Safecast/Safecast-Air/docs/gas_and_particulate/_static/3.JPG

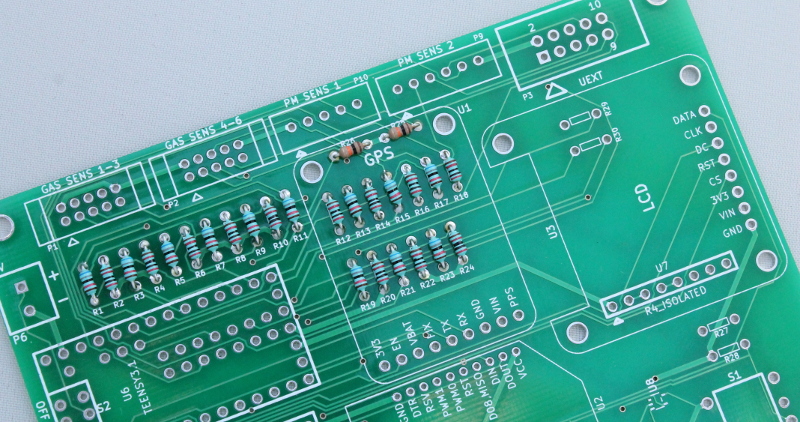
docs/gas_and_particulate/_static/3.JPG
