Safecast/Safecast-Air/docs/gas_and_particulate/_static/4.JPG

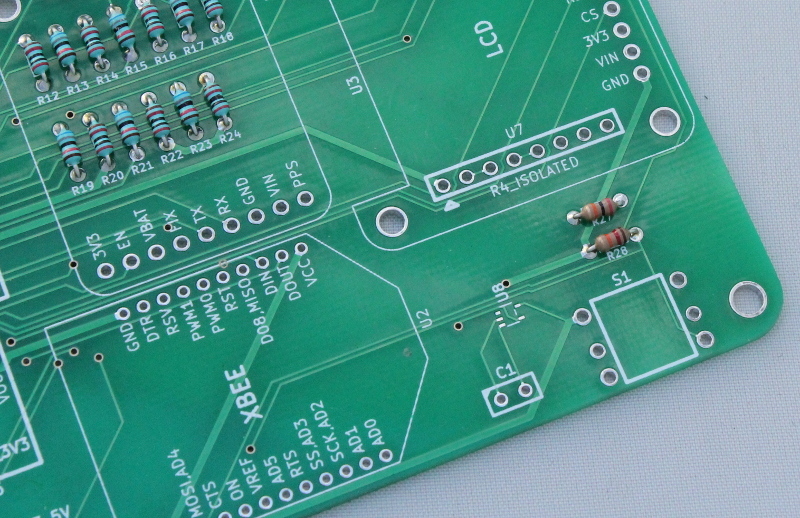
docs/gas_and_particulate/_static/4.JPG
