Safecast/Safecast-Air/docs/gas_and_particulate/_static/6.JPG

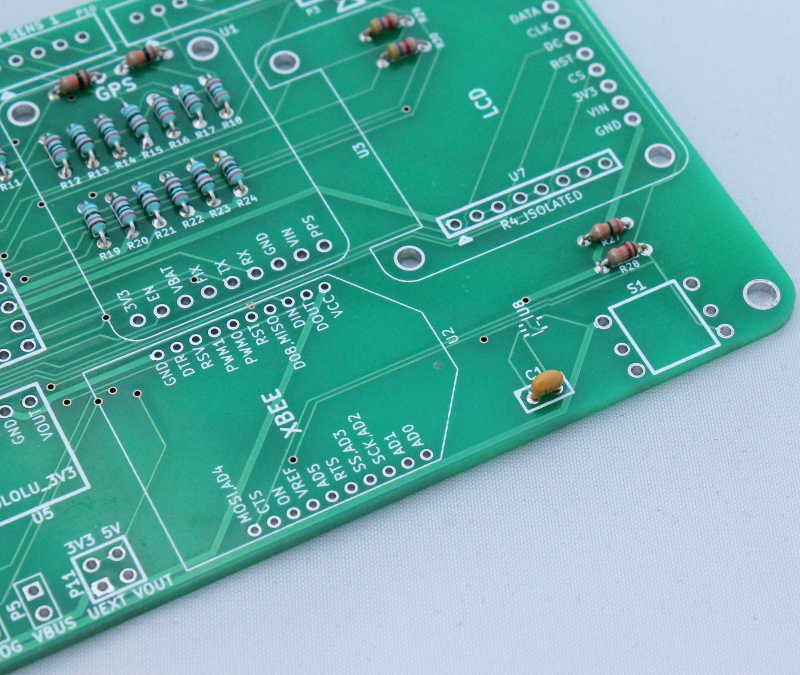
docs/gas_and_particulate/_static/6.JPG
