Safecast/Safecast-Air/docs/gas_and_particulate/_static/17c.JPG

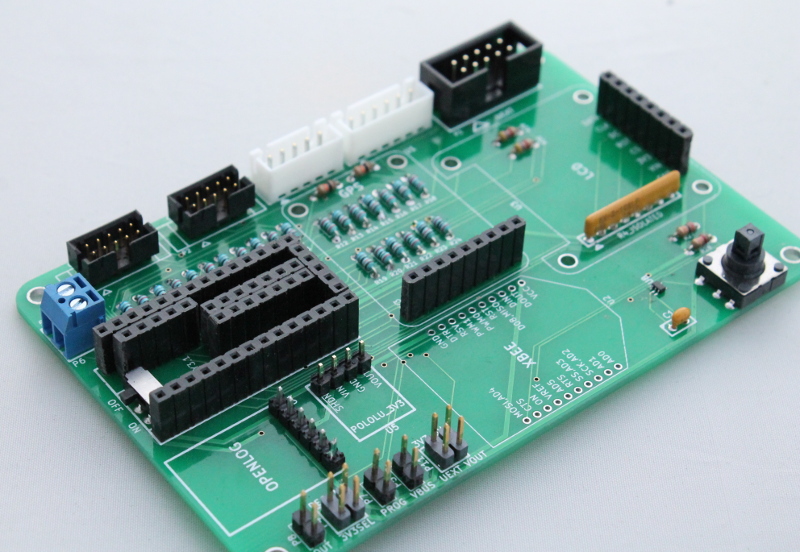
docs/gas_and_particulate/_static/17c.JPG
