Safecast/Safecast-Air/docs/gas_and_particulate/_static/21b.JPG

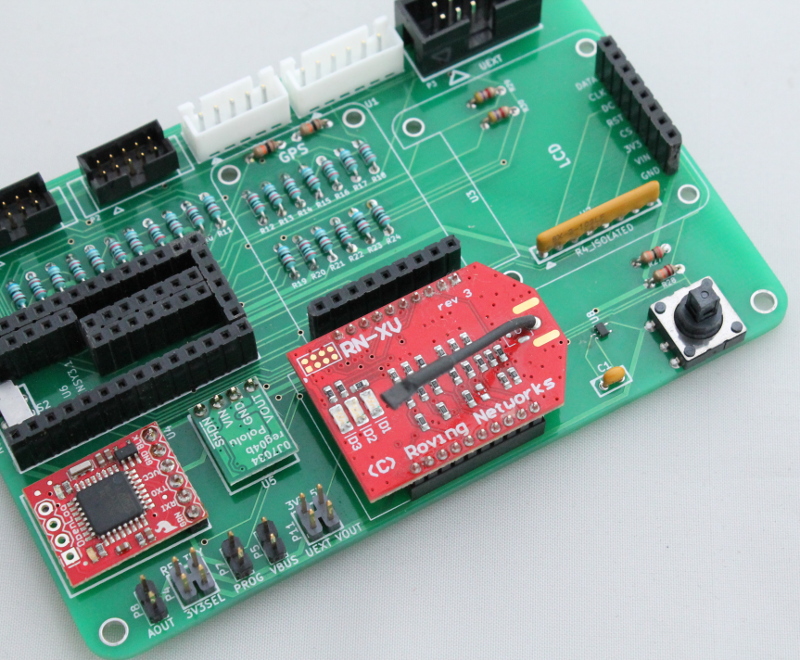
docs/gas_and_particulate/_static/21b.JPG
