Safecast/Safecast-Air/docs/gas_and_particulate/_static/alphasense_gas_1.png

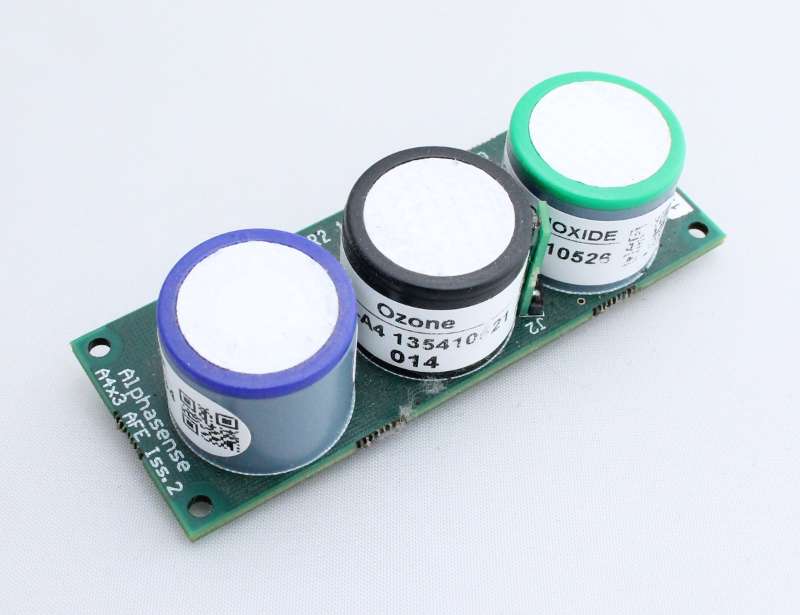
docs/gas_and_particulate/_static/alphasense_gas_1.png
