Safecast/Safecast-Air/docs/gas_and_particulate/_static/board_1.png

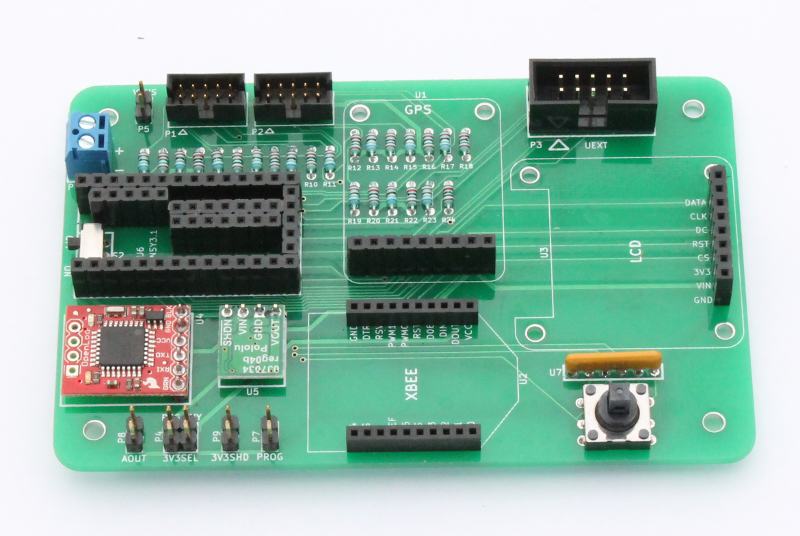
docs/gas_and_particulate/_static/board_1.png
