Safecast/Safecast-Air/docs/gas_and_particulate/_static/board_ver2.png

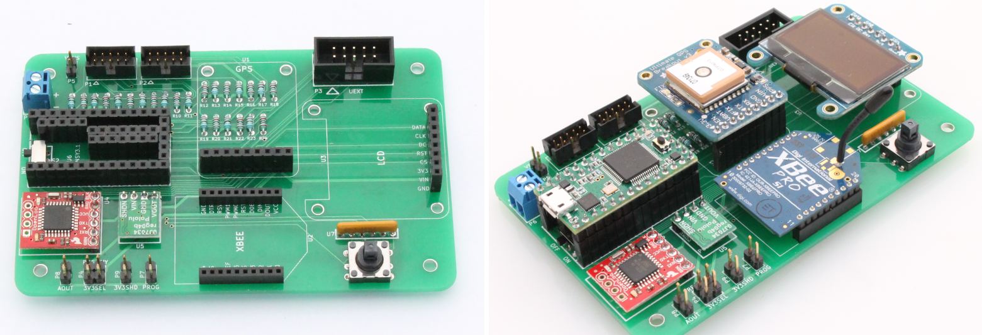
docs/gas_and_particulate/_static/board_ver2.png
