Safecast/Safecast-Air/docs/gas_and_particulate/_static/rev3_2.png

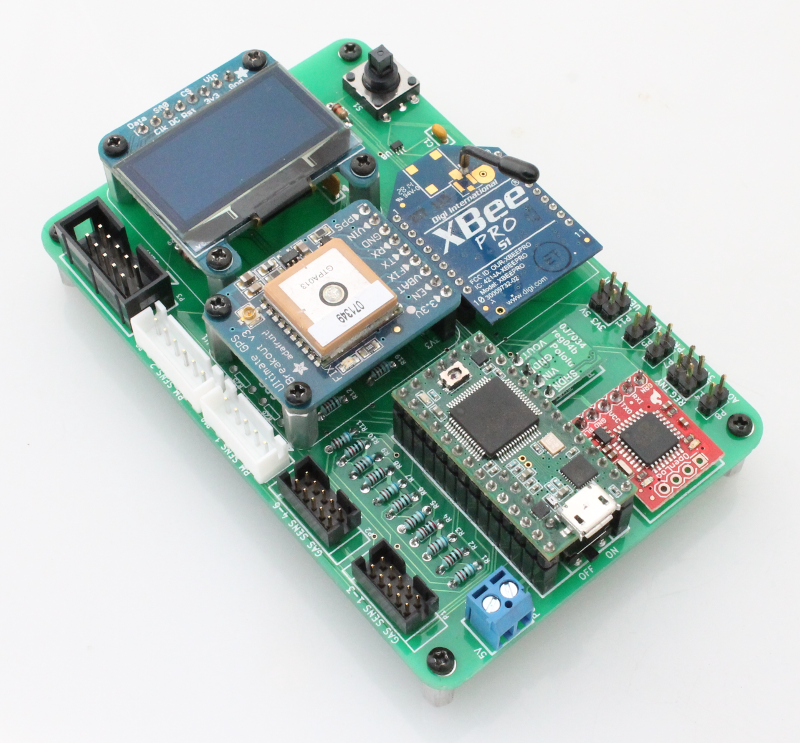
docs/gas_and_particulate/_static/rev3_2.png
