Safecast/Safecast-Air/docs/gas_and_particulate/_static/v4_7a.png

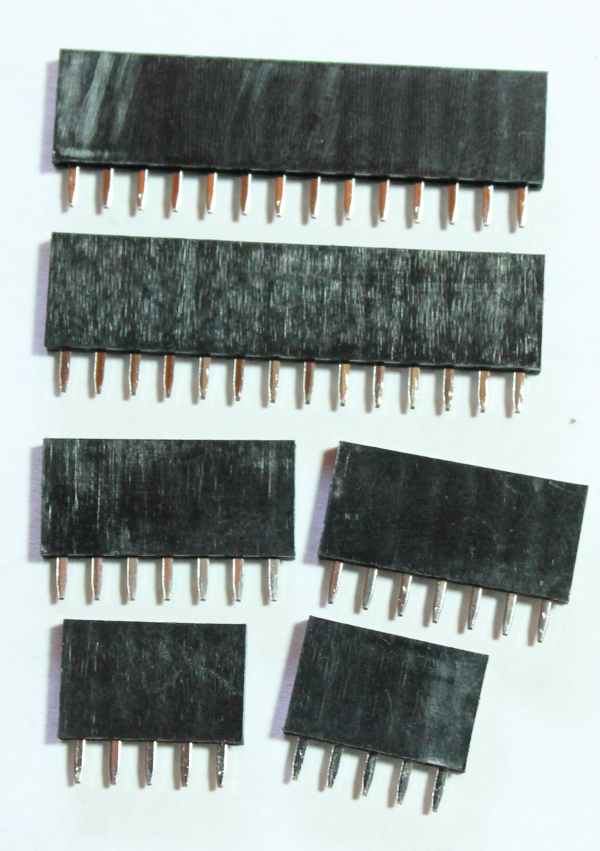
docs/gas_and_particulate/_static/v4_7a.png
