Safecast/Safecast-Air/images/about-arduino.png

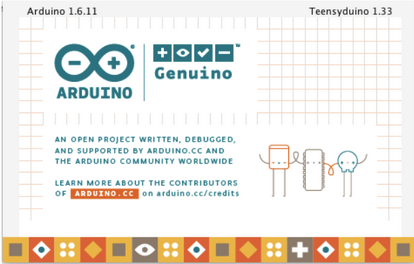
images/about-arduino.png
