Safecast/Safecast-Air/images/arduino.png

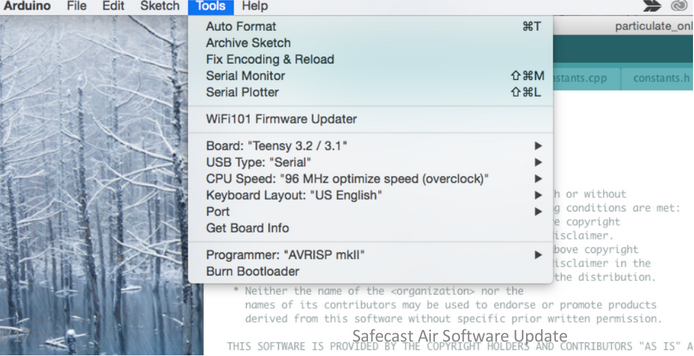
images/arduino.png
