Safecast/Safecast-Air/images/clone.png

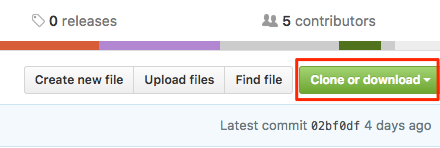
images/clone.png
