Safecast/Safecast-Air/images/electronics-assembly/schematic-small.png

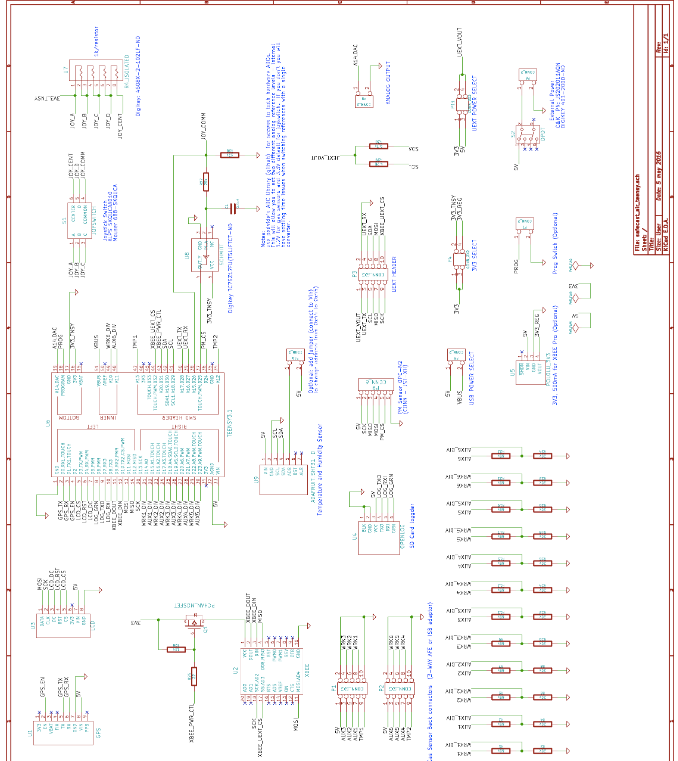
images/electronics-assembly/schematic-small.png
