Safecast/Safecast-Air/images/github-breadcrumb-link.png

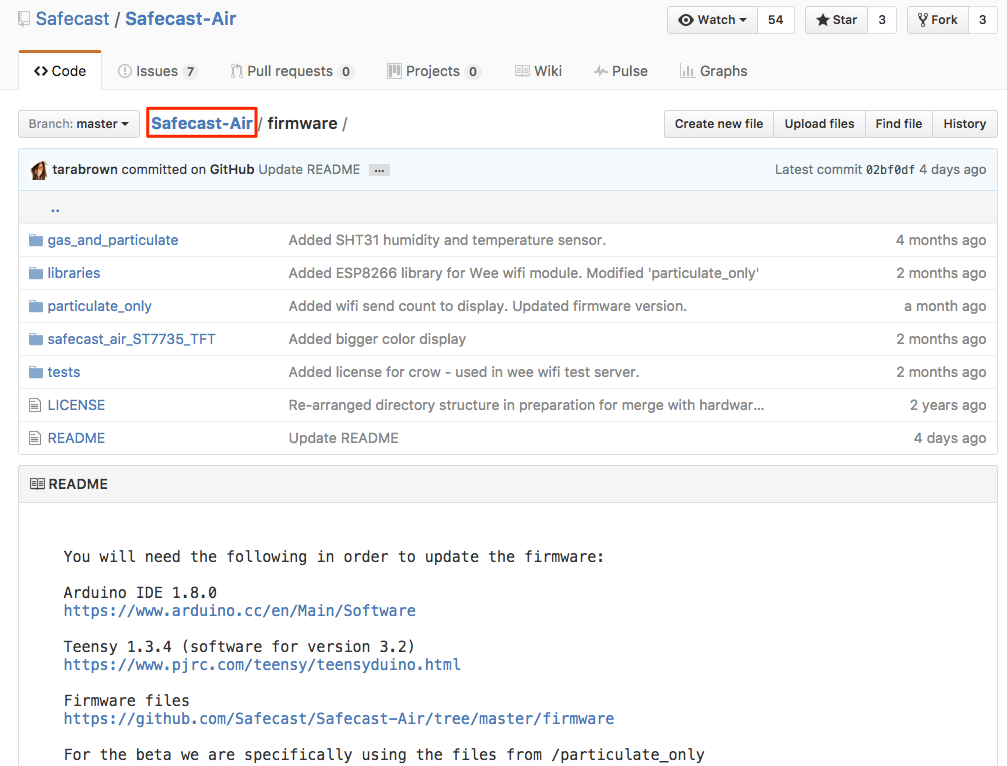
images/github-breadcrumb-link.png
