Safecast/Safecast-Air/images/log-file-detail.png

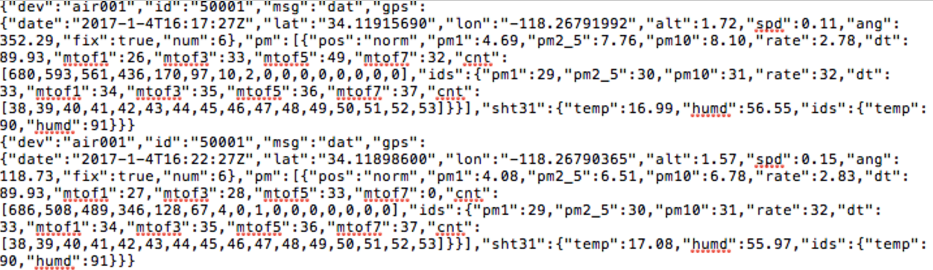
images/log-file-detail.png
