Safecast/Safecast-Air/images/log-files.png

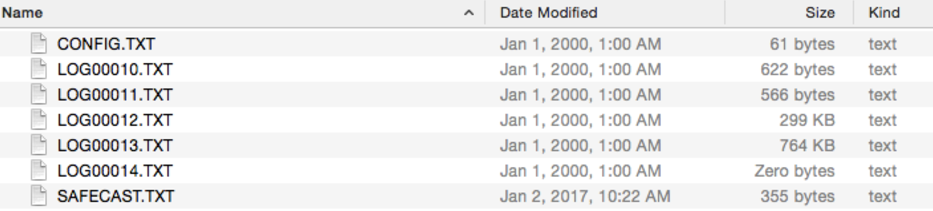
images/log-files.png
