Safecast/Safecast-Air/images/safecast-air-display.JPG

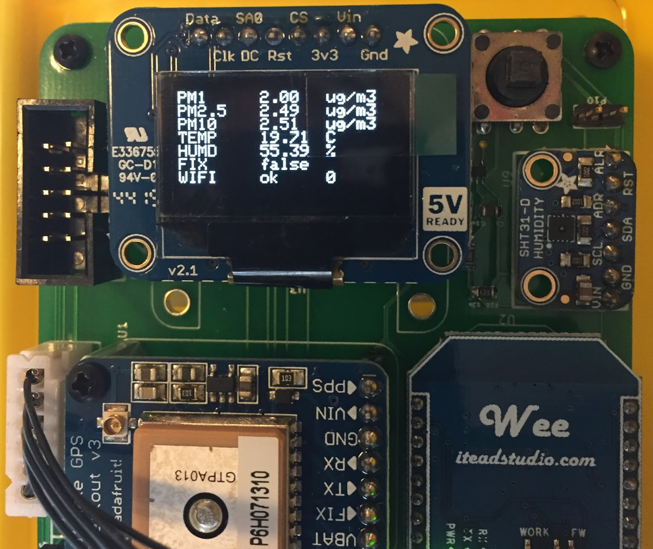
images/safecast-air-display.JPG
