Safecast/Safecast-Air/images/safecast-txt.png

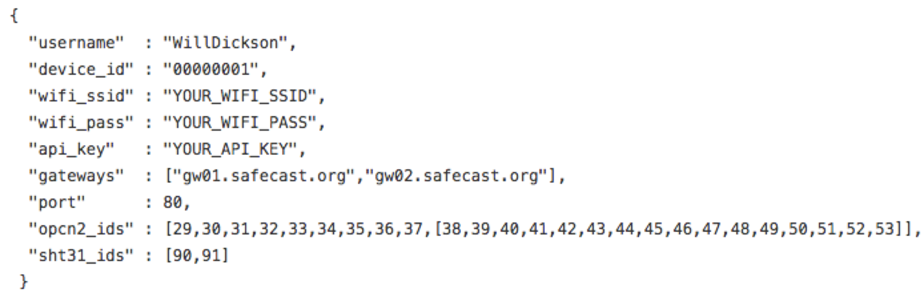
images/safecast-txt.png
