Safecast/Safecast-Air/images/safecast.png

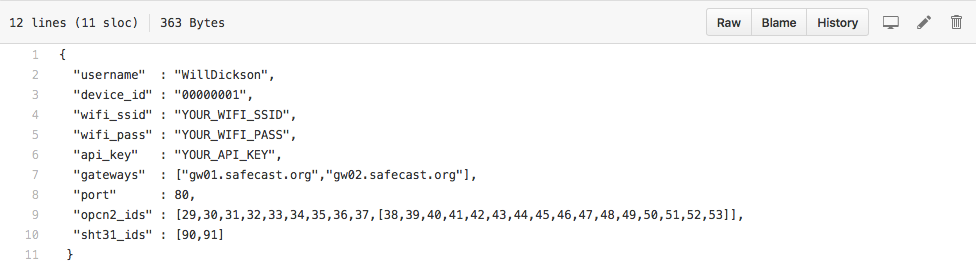
images/safecast.png
