Safecast/Safecast-Air/images/sketch.png

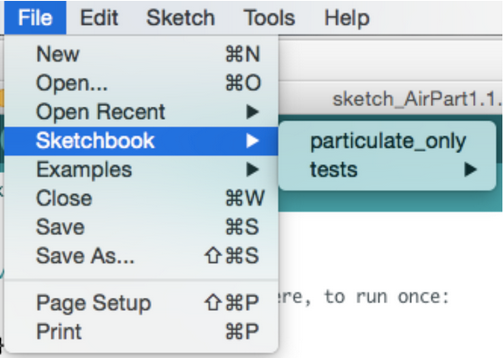
images/sketch.png
