Safecast/Safecast-Air/images/teensy-folders.png

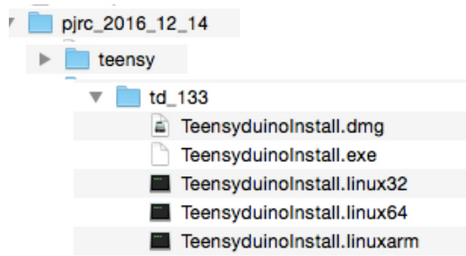
images/teensy-folders.png
