Safecast/Safecast-Air/images/teensy-tools-menu.png

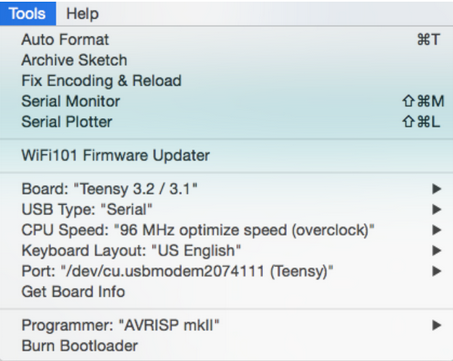
images/teensy-tools-menu.png
