Safecast/Safecast-Air/images/upload-sketch.png

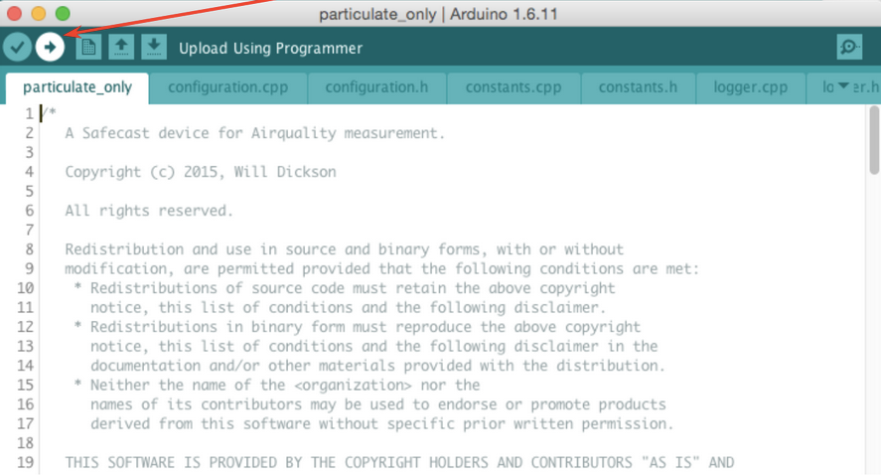
images/upload-sketch.png
