Safecast/Safecast-Air/images/usb.png

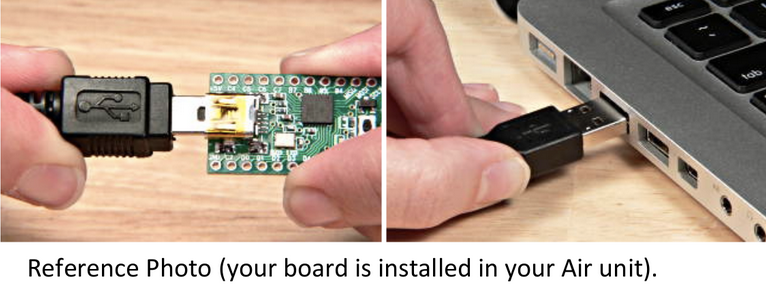
images/usb.png
