Safecast/Safecast-Air/images/zip.png

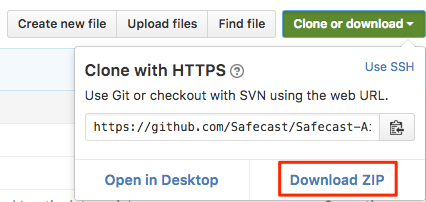
images/zip.png
