Safecast/Safecast-Air/images/electronics-assembly/main-board-first-set-components.png

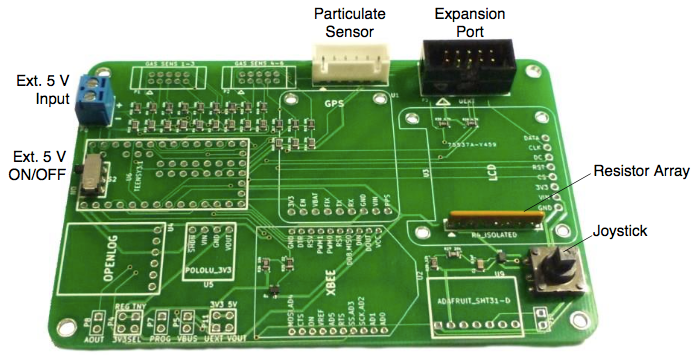
images/electronics-assembly/main-board-first-set-components.png
