Safecast/Safecast-Air/images/electronics-assembly/parts-bagged.png

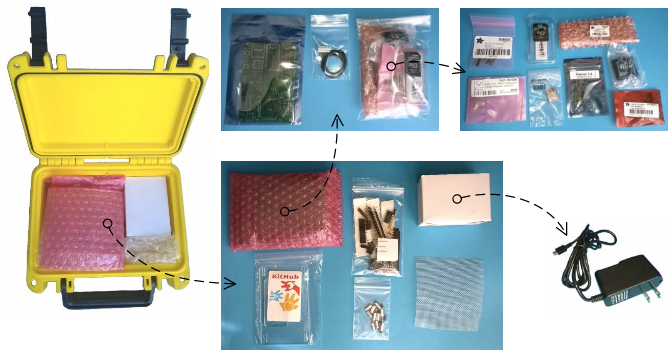
images/electronics-assembly/parts-bagged.png
