Safecast/Safecast-Air/hardware/enclosure/seahorse_120/methane_only/lower_insert/lower_insert.dxf

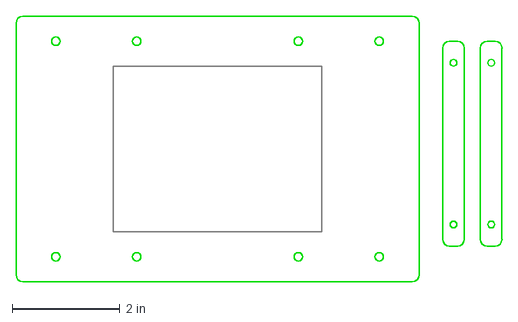
[picture p119: CAD file, 2016-02-19]
hardware/enclosure/seahorse_120/methane_only/lower_insert/lower_insert.dxf
9.02 x 4.92 in
