Safecast/Safecast-Air/hardware/enclosure/seahorse_120/methane_only/upper_insert/upper_insert.dxf

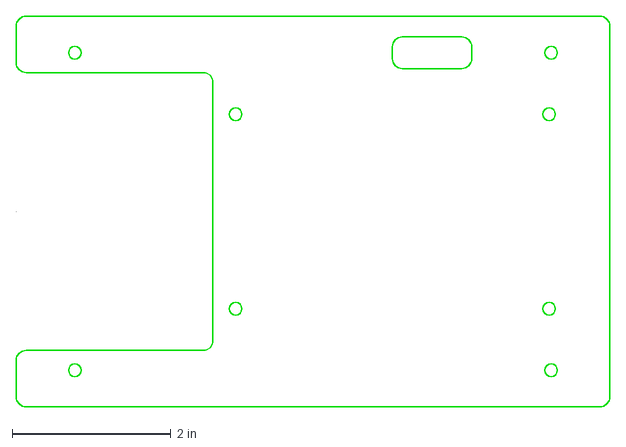
[picture p120: CAD file, 2016-02-19]
hardware/enclosure/seahorse_120/methane_only/upper_insert/upper_insert.dxf
7.48 x 4.92 in
