Safecast/Safecast-Air/hardware/enclosure/budind_nema_nbb/faraday/faraday_side_2.dxf

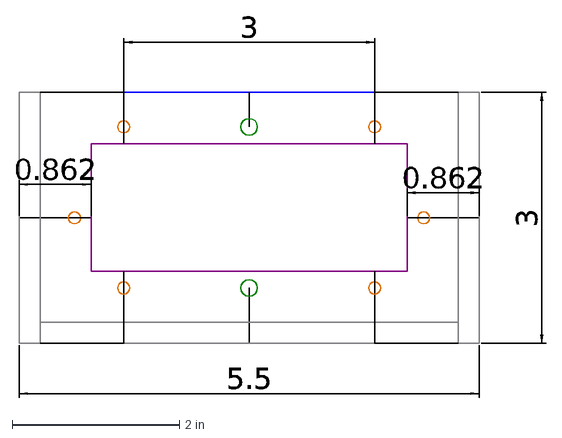
[picture p121: CAD file, 2015-12-14]
hardware/enclosure/budind_nema_nbb/faraday/faraday_side_2.dxf
5.5
3
0.862
