Safecast/Safecast-Air/hardware/enclosure/budind_nema_nbb/layouts/lasercutting/bottom_layout/pilot_template.dxf

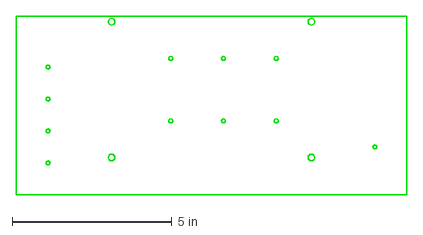
[picture p122: CAD file, 2015-09-15]
hardware/enclosure/budind_nema_nbb/layouts/lasercutting/bottom_layout/pilot_template.dxf
12.2 x 5.59 in
