Safecast/Safecast-Air/hardware/enclosure/layouts/isb_adaptor.dxf

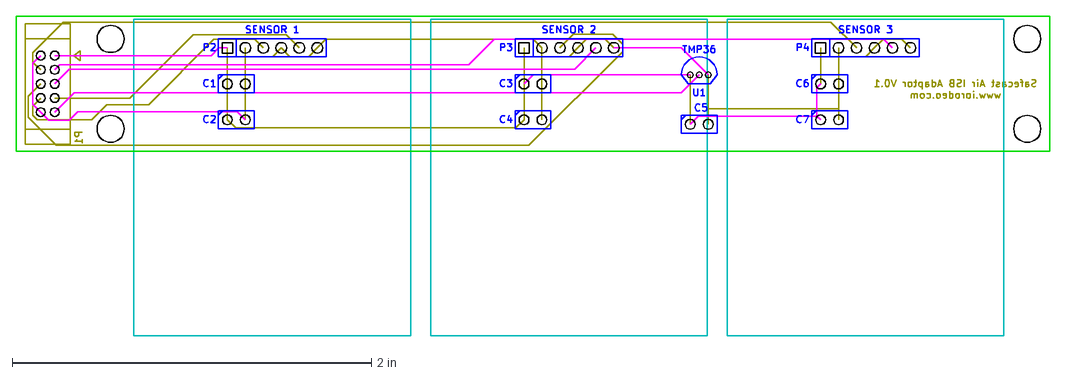
[picture p123: CAD file, 2015-06-25]
hardware/enclosure/layouts/isb_adaptor.dxf
5.75 x 1.77 in
