Safecast/Safecast-Air/hardware/enclosure/budind_nema_nbb/faraday/faraday_floor.dxf

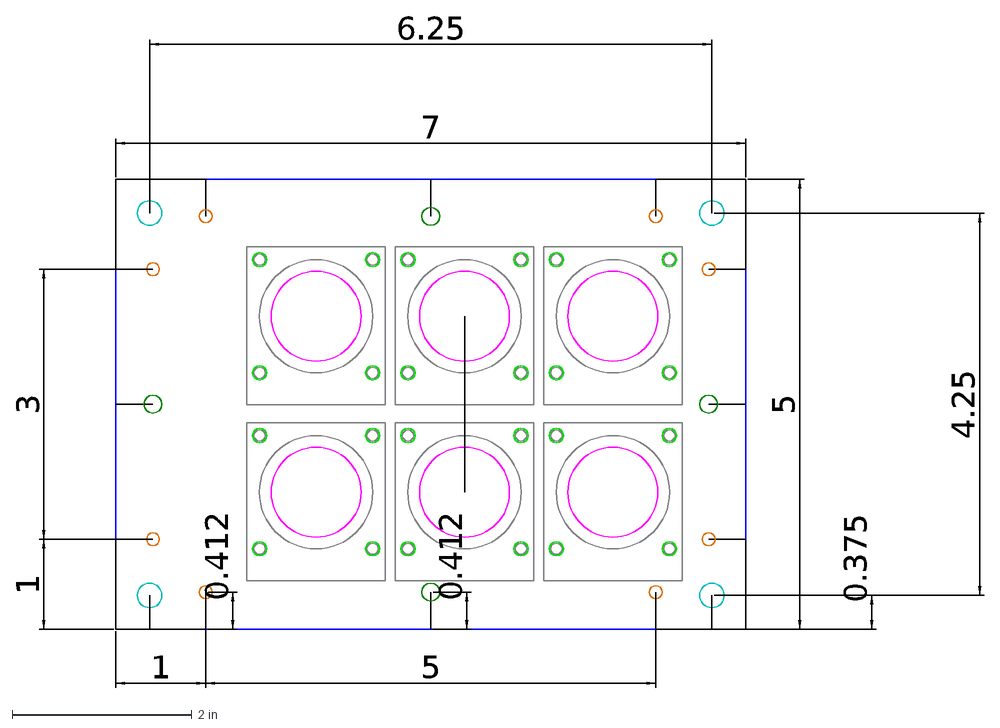
[picture p124: CAD file, 2015-09-15]
hardware/enclosure/budind_nema_nbb/faraday/faraday_floor.dxf
7
5
1
0.412
3
0.375
6.25
4.25
