Safecast/Safecast-Air/hardware/enclosure/budind_nema_nbb/layouts/lasercutting/bottom_layout/combined_template.dxf

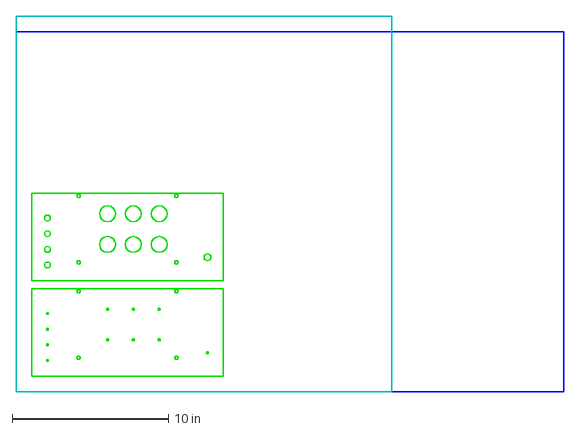
[picture p125: CAD file, 2015-09-15]
hardware/enclosure/budind_nema_nbb/layouts/lasercutting/bottom_layout/combined_template.dxf
35.0 x 24.0 in
