Safecast/Safecast-Air/hardware/enclosure/budind_nema_nbb/faraday/faraday_side_1.dxf

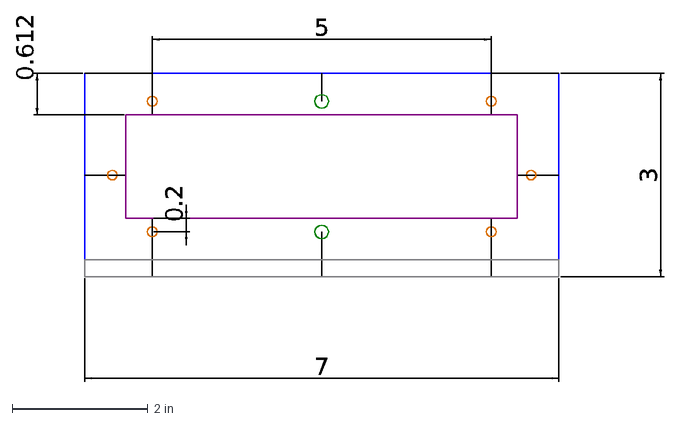
[picture p126: CAD file, 2015-09-01]
hardware/enclosure/budind_nema_nbb/faraday/faraday_side_1.dxf
3
7
0.2
5
0.612
