Safecast/Safecast-Air/hardware/enclosure/budind_nema_nbb/faraday/faraday_mesh_upper.dxf

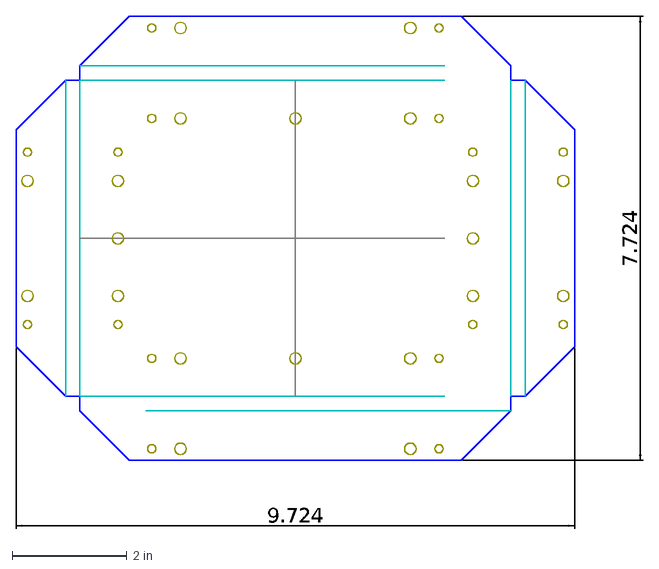
[picture p127: CAD file, 2015-09-01]
hardware/enclosure/budind_nema_nbb/faraday/faraday_mesh_upper.dxf
7.724
9.724
