Safecast/Safecast-Air/hardware/enclosure/budind_nema_nbb/faraday/faraday_mesh_lower.dxf

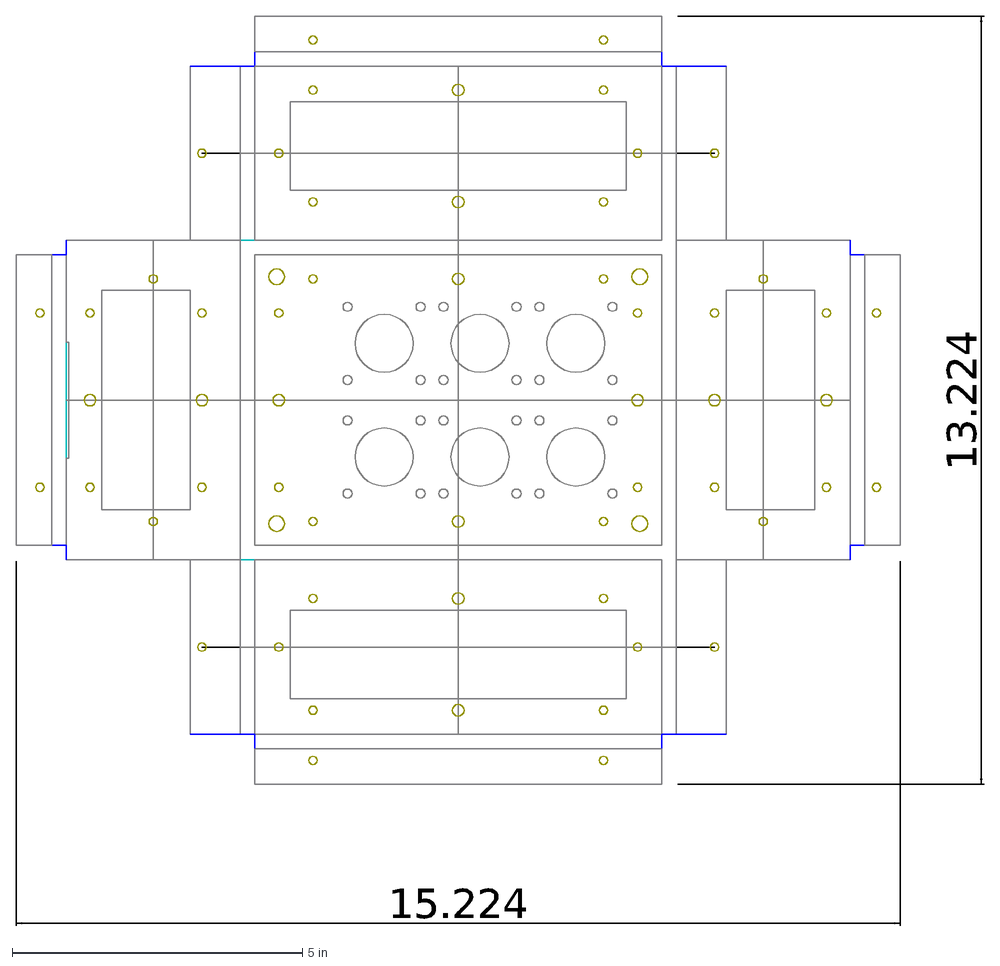
[picture p128: CAD file, 2015-08-30]
hardware/enclosure/budind_nema_nbb/faraday/faraday_mesh_lower.dxf
13.224
15.224
