Safecast/Safecast-Air/hardware/enclosure/budind_nema_nbb/faraday/faraday_side_3.dxf

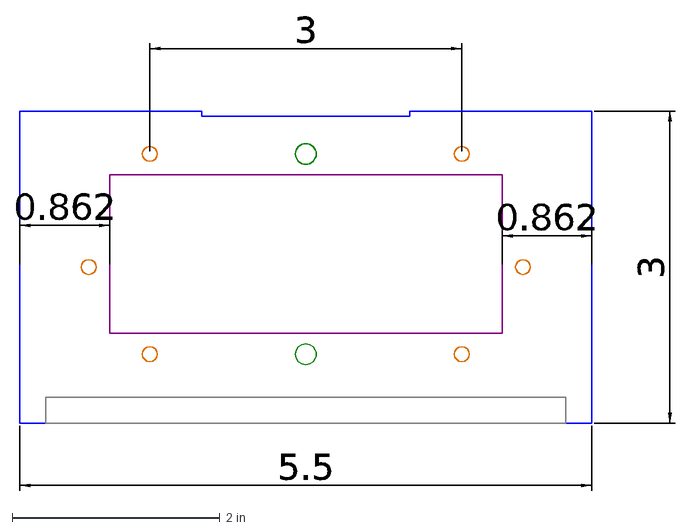
[picture p129: CAD file, 2015-08-30]
hardware/enclosure/budind_nema_nbb/faraday/faraday_side_3.dxf
5.5
3
0.862
