Safecast/Safecast-Air/hardware/enclosure/budind_nema_nbb/faraday/isb_footprint.dxf

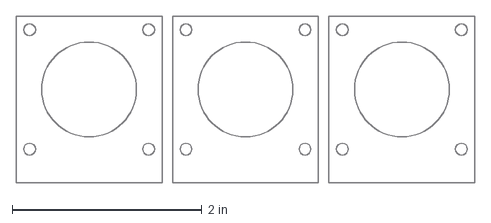
[picture p130: CAD file, 2015-08-06]
hardware/enclosure/budind_nema_nbb/faraday/isb_footprint.dxf
4.84 x 1.76 in
