Safecast/Safecast-Air/images/electronics-assembly/5v.png

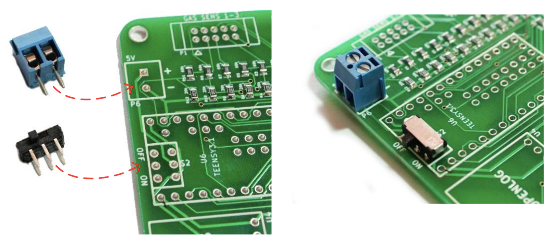
images/electronics-assembly/5v.png
