Safecast/Safecast-Air/images/electronics-assembly/14pos-headers-in-place.png

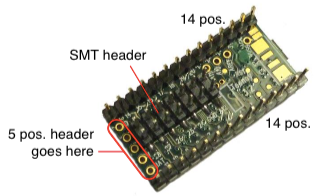
images/electronics-assembly/14pos-headers-in-place.png
