Safecast/Safecast-Air/images/electronics-assembly/ac wires-secured-with-a-cable-tie.png

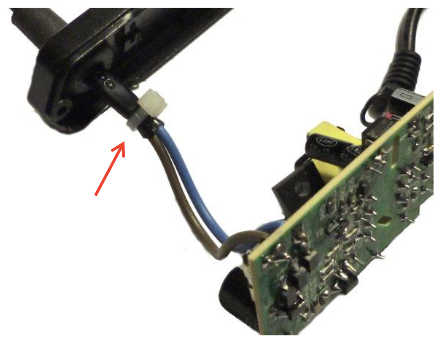
images/electronics-assembly/ac wires-secured-with-a-cable-tie.png
