Safecast/Safecast-Air/images/electronics-assembly/ac-power-cord-with-2-pin-Europlug.png

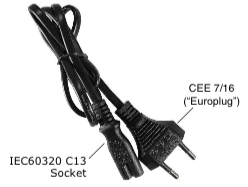
images/electronics-assembly/ac-power-cord-with-2-pin-Europlug.png
