Safecast/Safecast-Air/images/electronics-assembly/ac-wires-removed-from-PCB.png

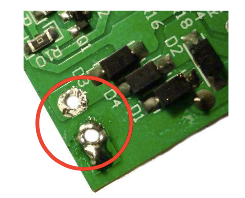
images/electronics-assembly/ac-wires-removed-from-PCB.png
