Safecast/Safecast-Air/images/electronics-assembly/adafruit-temp-humidity.png

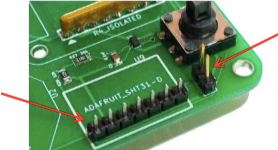
images/electronics-assembly/adafruit-temp-humidity.png
