Safecast/Safecast-Air/images/electronics-assembly/battery-clip-soldering.png

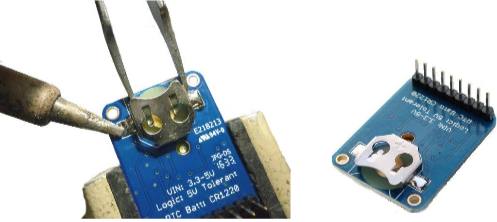
images/electronics-assembly/battery-clip-soldering.png
