Safecast/Safecast-Air/images/electronics-assembly/blades-removal-steps.png

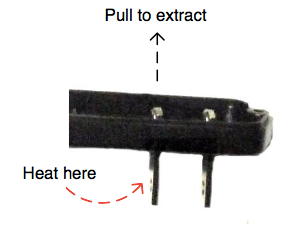
images/electronics-assembly/blades-removal-steps.png
