Safecast/Safecast-Air/images/electronics-assembly/cleaned-pcb.png

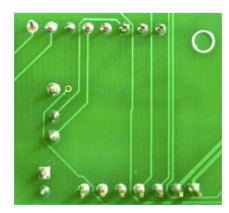
images/electronics-assembly/cleaned-pcb.png
