Safecast/Safecast-Air/images/electronics-assembly/completed-teensy-board.png

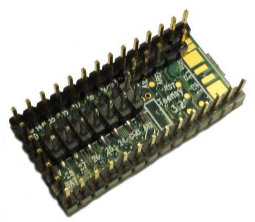
images/electronics-assembly/completed-teensy-board.png
