Safecast/Safecast-Air/images/electronics-assembly/config-presetting-headers-pcb-pos.png

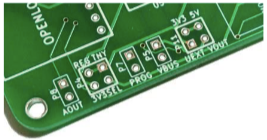
images/electronics-assembly/config-presetting-headers-pcb-pos.png
