Safecast/Safecast-Air/images/electronics-assembly/configuration-headers-in-place.png

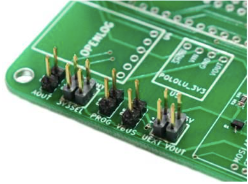
images/electronics-assembly/configuration-headers-in-place.png
