Safecast/Safecast-Air/images/electronics-assembly/cutting-away-the-socket.png

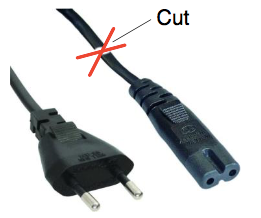
images/electronics-assembly/cutting-away-the-socket.png
