Safecast/Safecast-Air/images/electronics-assembly/cutting-straight-headers.png

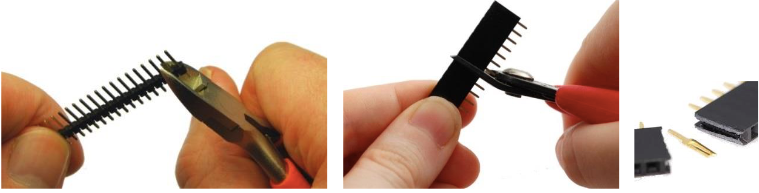
images/electronics-assembly/cutting-straight-headers.png
