Safecast/Safecast-Air/images/electronics-assembly/finished-board.png

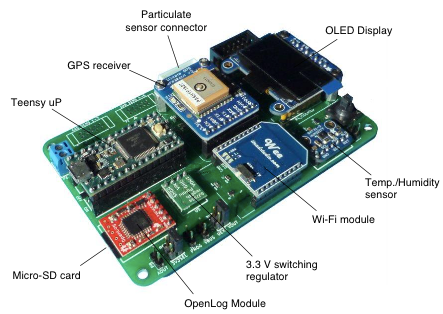
images/electronics-assembly/finished-board.png
