Safecast/Safecast-Air/images/electronics-assembly/gps-board-with-headers-back.png

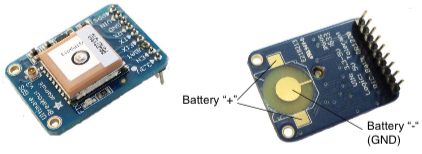
images/electronics-assembly/gps-board-with-headers-back.png
