Safecast/Safecast-Air/images/electronics-assembly/gps-complete-kit.png

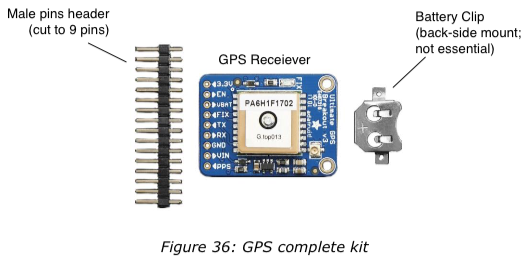
images/electronics-assembly/gps-complete-kit.png
