Safecast/Safecast-Air/images/electronics-assembly/gps-module-mounted.png

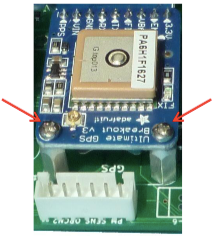
images/electronics-assembly/gps-module-mounted.png
