Safecast/Safecast-Air/images/electronics-assembly/gps-mounting.png

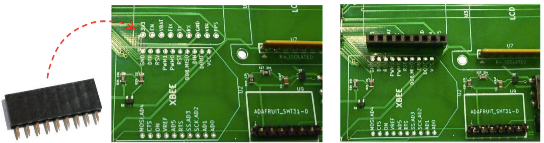
images/electronics-assembly/gps-mounting.png
