Safecast/Safecast-Air/images/electronics-assembly/Installed-OLED-Display.png

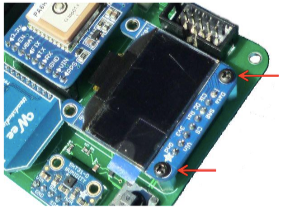
images/electronics-assembly/Installed-OLED-Display.png
