Safecast/Safecast-Air/images/electronics-assembly/main-board-mounted-on-acrylic-plate.png

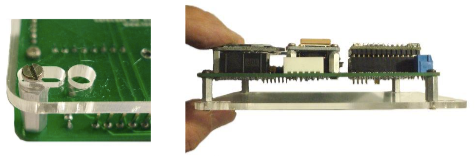
images/electronics-assembly/main-board-mounted-on-acrylic-plate.png
