Safecast/Safecast-Air/images/electronics-assembly/main-board-with-standoffs.png

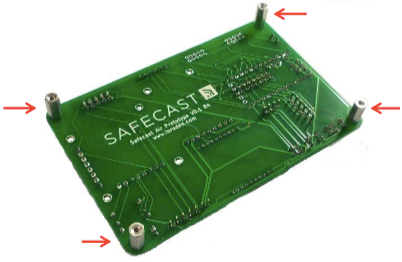
images/electronics-assembly/main-board-with-standoffs.png
