Safecast/Safecast-Air/images/electronics-assembly/main-pcb-layout.png

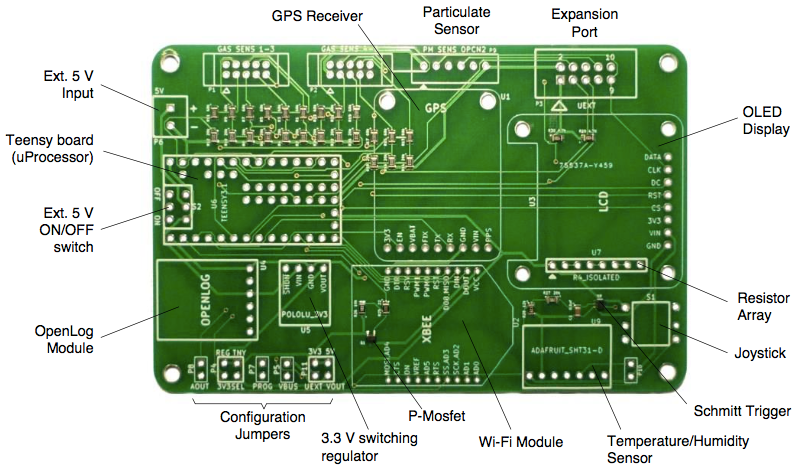
images/electronics-assembly/main-pcb-layout.png
