Safecast/Safecast-Air/images/electronics-assembly/misaligned-end-header.png

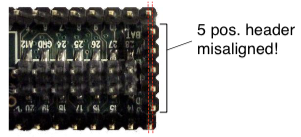
images/electronics-assembly/misaligned-end-header.png
