Safecast/Safecast-Air/images/electronics-assembly/mod-5pos-fem-header-soldered.png

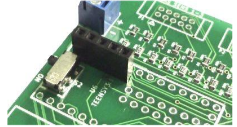
images/electronics-assembly/mod-5pos-fem-header-soldered.png
