Safecast/Safecast-Air/images/electronics-assembly/mounting-the-cable-protection-grommet.png

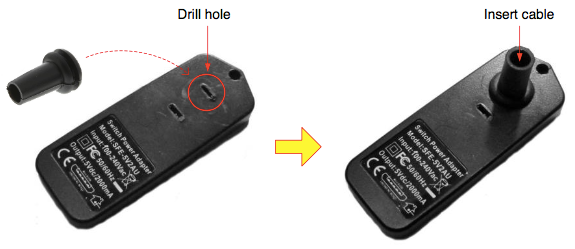
images/electronics-assembly/mounting-the-cable-protection-grommet.png
