Safecast/Safecast-Air/images/electronics-assembly/oled-display-8pos-male.png

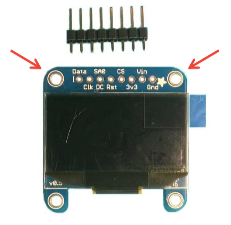
images/electronics-assembly/oled-display-8pos-male.png
