Safecast/Safecast-Air/images/electronics-assembly/oled-mounting.png

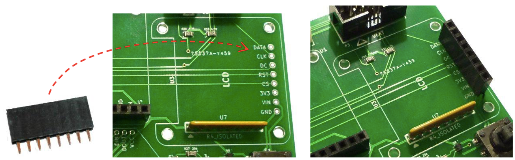
images/electronics-assembly/oled-mounting.png
