Safecast/Safecast-Air/images/electronics-assembly/Opened-SFE-5V2AU-Wall-Adapter.png

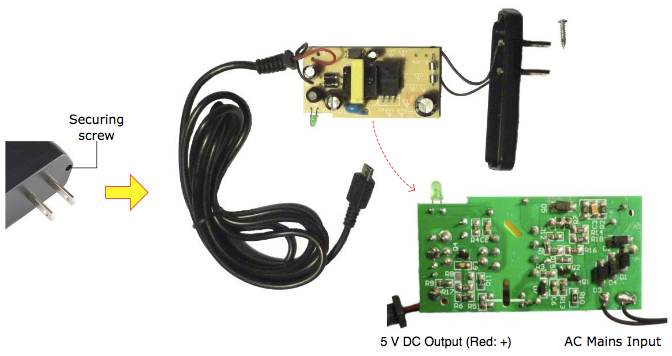
images/electronics-assembly/Opened-SFE-5V2AU-Wall-Adapter.png
