Safecast/Safecast-Air/images/electronics-assembly/openlog-headers.png

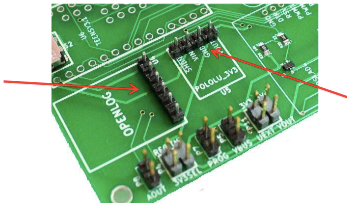
images/electronics-assembly/openlog-headers.png
