Safecast/Safecast-Air/images/electronics-assembly/openlog-unit.png

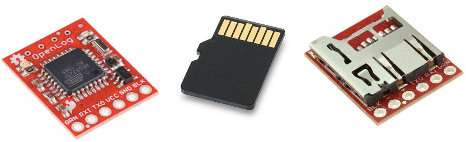
images/electronics-assembly/openlog-unit.png
