Safecast/Safecast-Air/images/electronics-assembly/pbc-layout.png

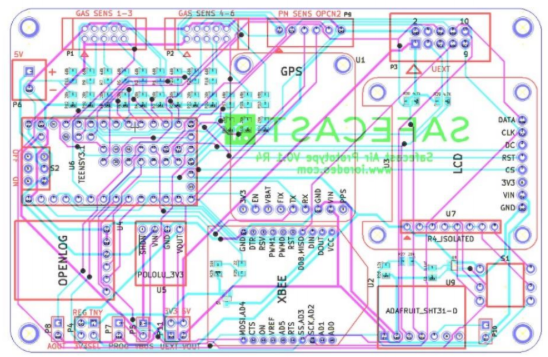
images/electronics-assembly/pbc-layout.png
