Safecast/Safecast-Air/images/electronics-assembly/pcb-cleaning-kits.png

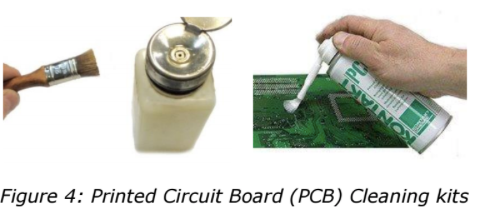
images/electronics-assembly/pcb-cleaning-kits.png
