Safecast/Safecast-Air/images/electronics-assembly/pin-headers-placement-guide.png

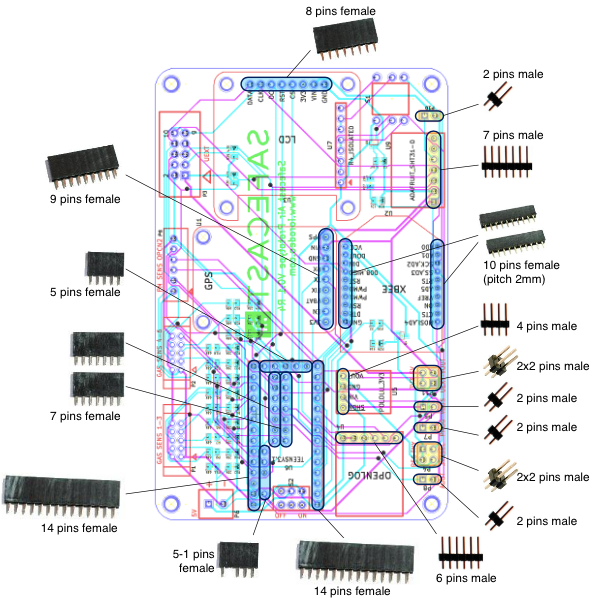
images/electronics-assembly/pin-headers-placement-guide.png
