Safecast/Safecast-Air/images/electronics-assembly/pin-removal.png

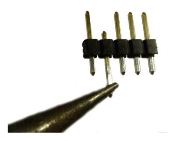
images/electronics-assembly/pin-removal.png
