Safecast/Safecast-Air/images/electronics-assembly/place-for-modified-5pin-header.png

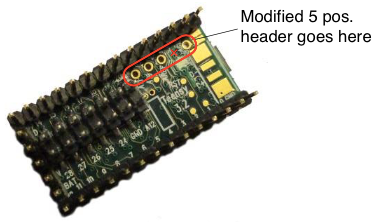
images/electronics-assembly/place-for-modified-5pin-header.png
