Safecast/Safecast-Air/images/electronics-assembly/Placement-Guide-for-Breakout-Modules.png

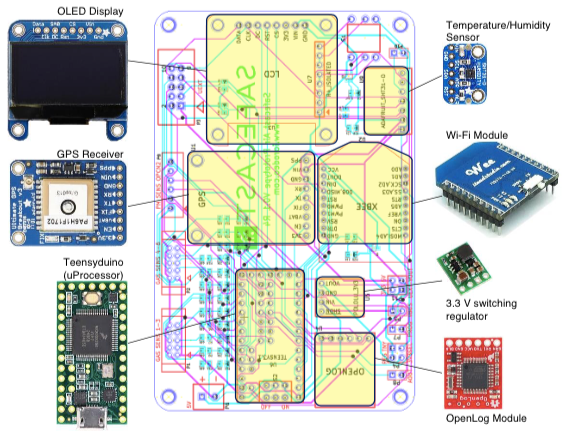
images/electronics-assembly/Placement-Guide-for-Breakout-Modules.png
