Safecast/Safecast-Air/images/electronics-assembly/Placement-guide-for-Configuration-Headers.png

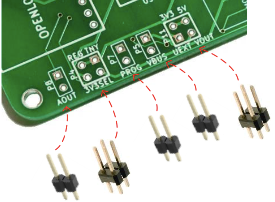
images/electronics-assembly/Placement-guide-for-Configuration-Headers.png
