Safecast/Safecast-Air/images/electronics-assembly/placement-shrouded-headers.png

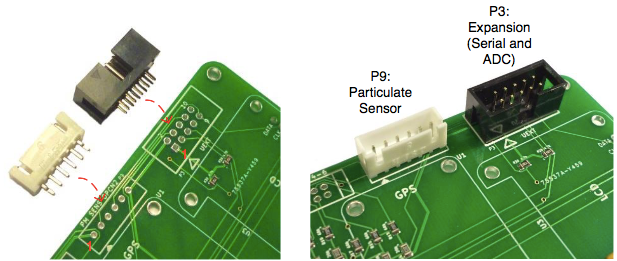
images/electronics-assembly/placement-shrouded-headers.png
