Safecast/Safecast-Air/images/electronics-assembly/pre-tinning-smt.png

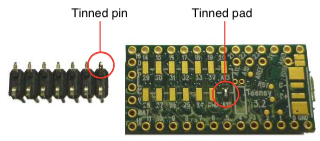
images/electronics-assembly/pre-tinning-smt.png
