Safecast/Safecast-Air/images/electronics-assembly/prepared-breakout-headers.png

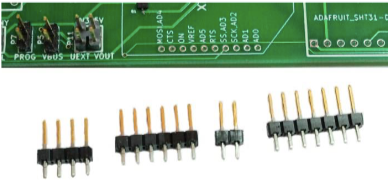
images/electronics-assembly/prepared-breakout-headers.png
