Safecast/Safecast-Air/images/electronics-assembly/Preparing-the-AC-cord.png

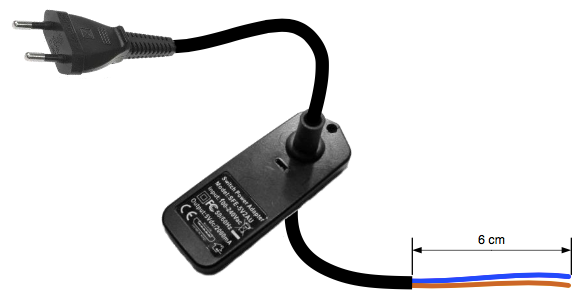
images/electronics-assembly/Preparing-the-AC-cord.png
