Safecast/Safecast-Air/images/electronics-assembly/preparing-the-battery-clip-mount.png

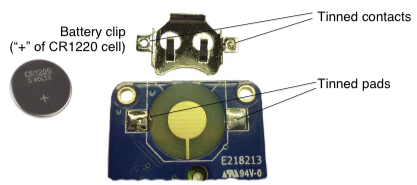
images/electronics-assembly/preparing-the-battery-clip-mount.png
