Safecast/Safecast-Air/images/electronics-assembly/remov-1pin-leg-5pos-female-header.png

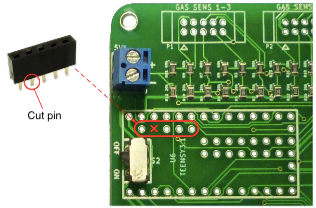
images/electronics-assembly/remov-1pin-leg-5pos-female-header.png
