Safecast/Safecast-Air/images/electronics-assembly/resistorarray-toggleswitch-soldering.png

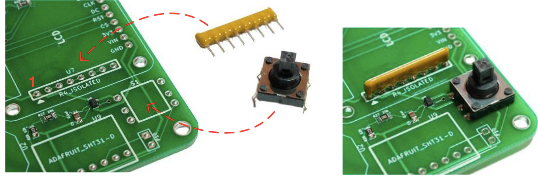
images/electronics-assembly/resistorarray-toggleswitch-soldering.png
