Safecast/Safecast-Air/images/electronics-assembly/rubber-grommets-with-sleeve.png

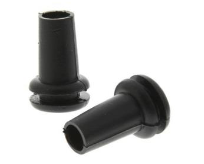
images/electronics-assembly/rubber-grommets-with-sleeve.png
