Safecast/Safecast-Air/images/electronics-assembly/shipped-sep.png

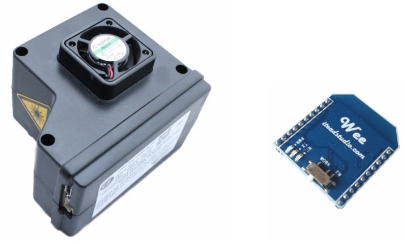
images/electronics-assembly/shipped-sep.png
