Safecast/Safecast-Air/images/electronics-assembly/SMT-header-soldered.png

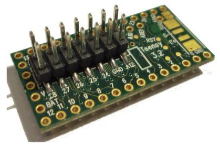
images/electronics-assembly/SMT-header-soldered.png
