Safecast/Safecast-Air/images/electronics-assembly/solder-joint-examples.png

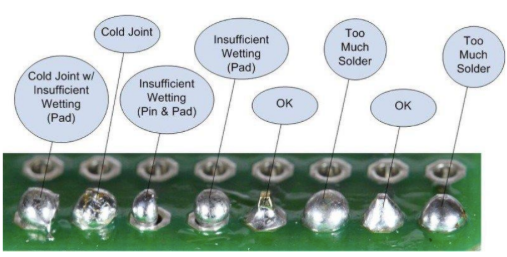
images/electronics-assembly/solder-joint-examples.png
