Safecast/Safecast-Air/images/electronics-assembly/Soldering-the-AC-wires-to-the-PCB.png

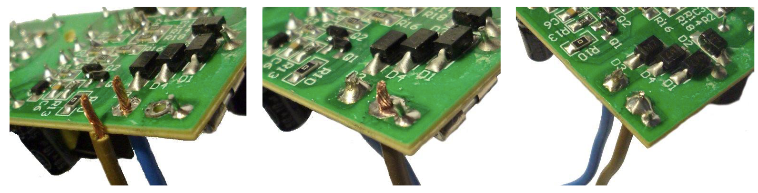
images/electronics-assembly/Soldering-the-AC-wires-to-the-PCB.png
