Safecast/Safecast-Air/images/electronics-assembly/switching-regulator-soldered.png

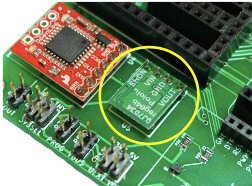
images/electronics-assembly/switching-regulator-soldered.png
