Safecast/Safecast-Air/images/electronics-assembly/teensy-conn-female-headers.png

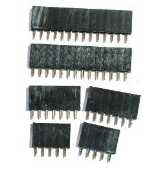
images/electronics-assembly/teensy-conn-female-headers.png
