Safecast/Safecast-Air/images/electronics-assembly/teensy-sockets-mounting-steps.png

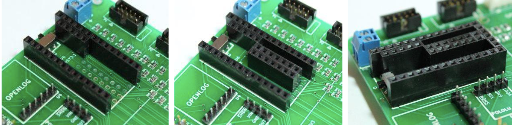
images/electronics-assembly/teensy-sockets-mounting-steps.png
