Safecast/Safecast-Air/images/electronics-assembly/temp-humid-sensor-soldered.png

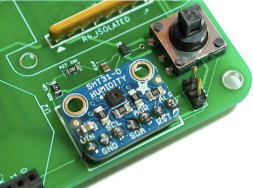
images/electronics-assembly/temp-humid-sensor-soldered.png
