Safecast/Safecast-Air/images/electronics-assembly/thinning-the-5pos-end-header.png

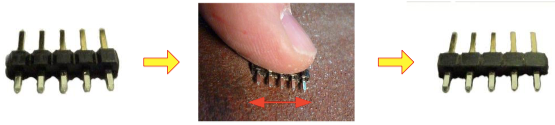
images/electronics-assembly/thinning-the-5pos-end-header.png
