Safecast/Safecast-Air/images/electronics-assembly/Trimming-the-SMT-header-case.png

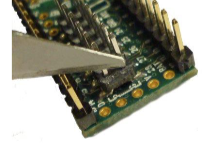
images/electronics-assembly/Trimming-the-SMT-header-case.png
