Safecast/Safecast-Air/images/electronics-assembly/wall-adapter-with-PCB-back-in-place.png

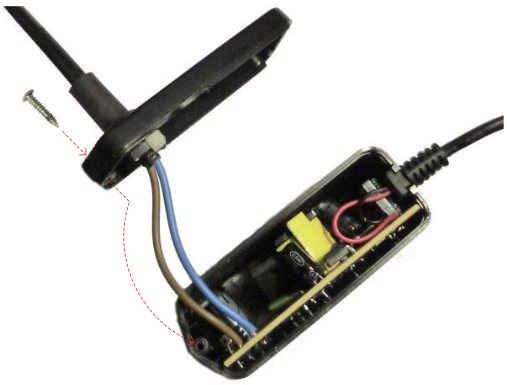
images/electronics-assembly/wall-adapter-with-PCB-back-in-place.png
