Safecast/Safecast-Air/images/electronics-assembly/wall-adaptor-and-europlug.png

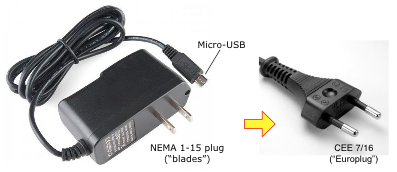
images/electronics-assembly/wall-adaptor-and-europlug.png
