Safecast/Safecast-Air/images/electronics-assembly/wee-mounting.png

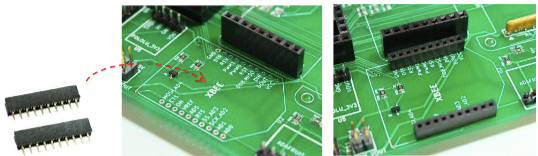
images/electronics-assembly/wee-mounting.png
