Safecast/Safecast-Air/images/electronics-assembly/wifi-module-in-place.png

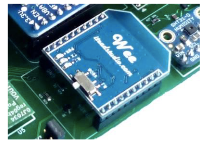
images/electronics-assembly/wifi-module-in-place.png
