Safecast/Safecast-Air/images/hardware-instructions/1.png

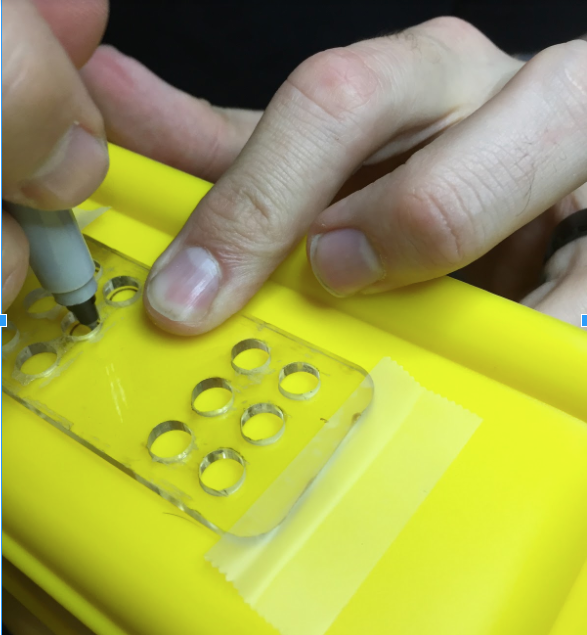
images/hardware-instructions/1.png
