Safecast/Safecast-Air/images/hardware-instructions/2.png

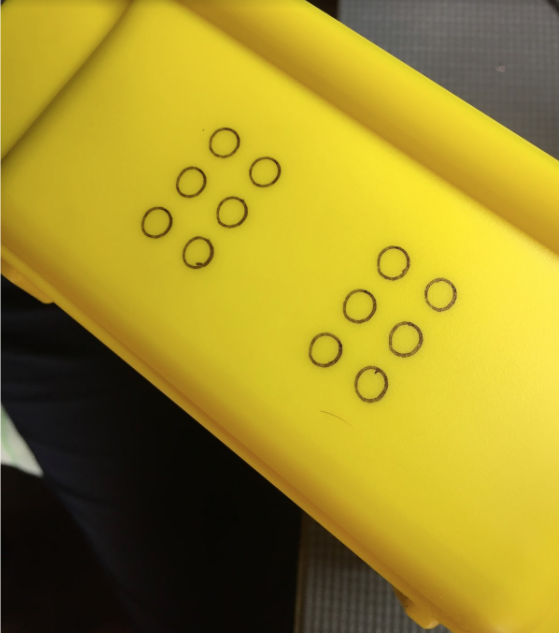
images/hardware-instructions/2.png
