Safecast/Safecast-Air/images/hardware-instructions/3.png

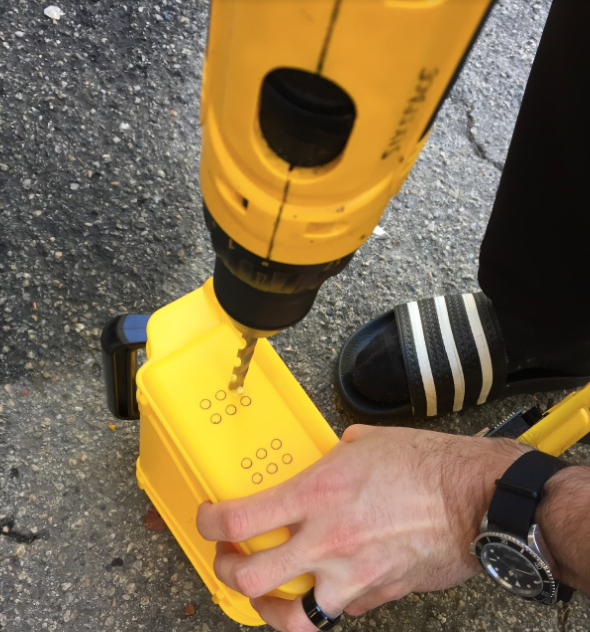
images/hardware-instructions/3.png
