Safecast/Safecast-Air/images/hardware-instructions/4.png

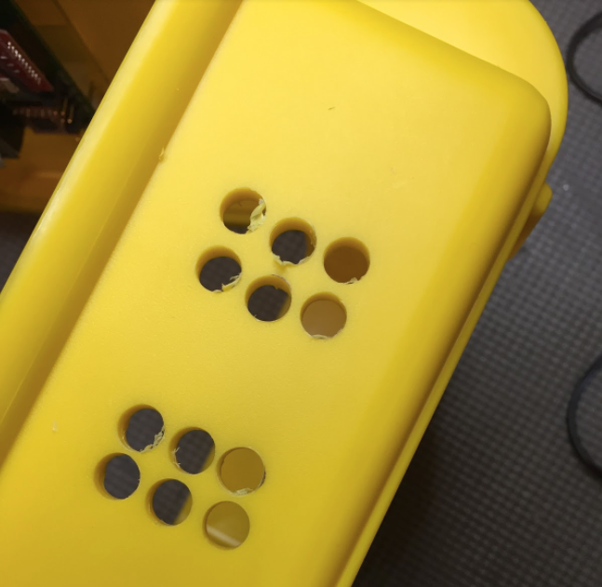
images/hardware-instructions/4.png
