Safecast/Safecast-Air/images/hardware-instructions/5.png

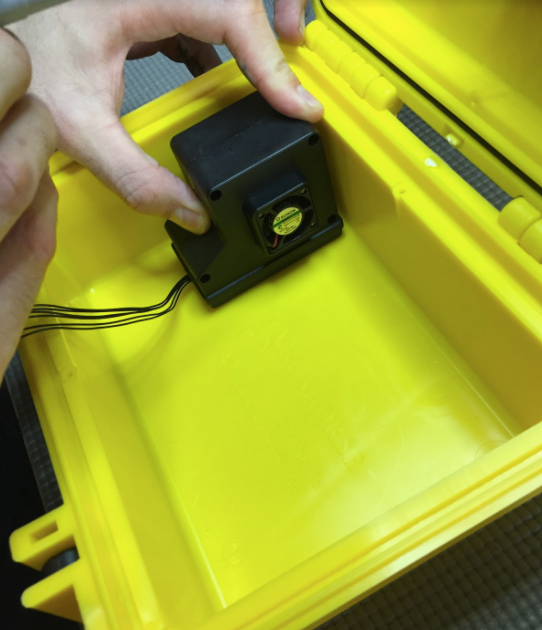
images/hardware-instructions/5.png
