Safecast/Safecast-Air/images/hardware-instructions/6.png

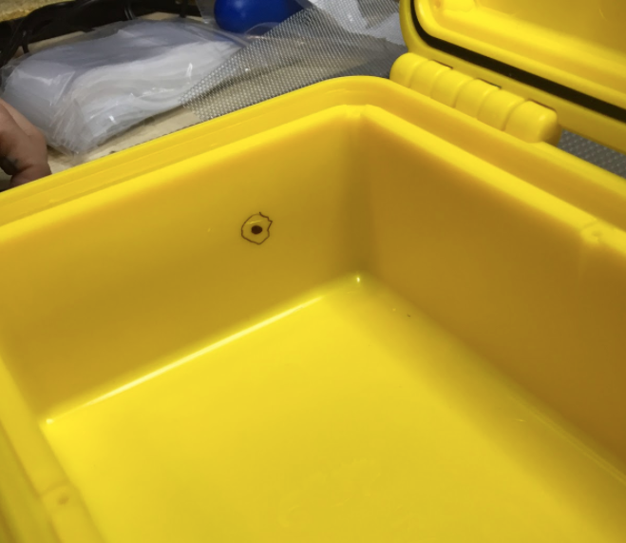
images/hardware-instructions/6.png
