Safecast/Safecast-Air/images/hardware-instructions/7.png

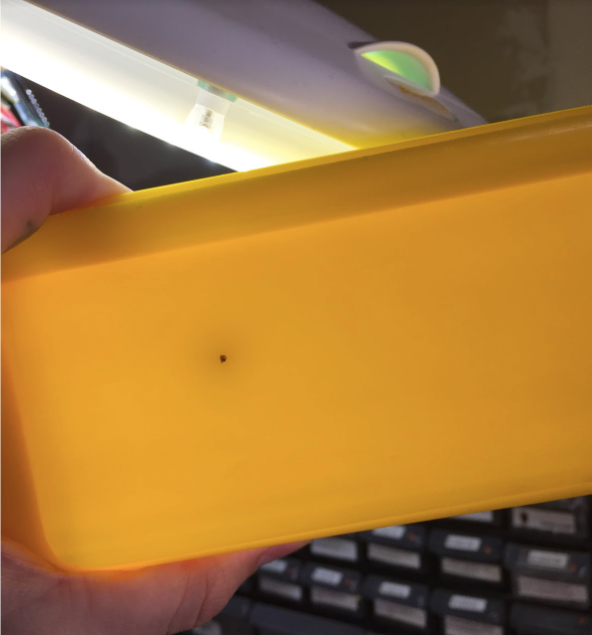
images/hardware-instructions/7.png
