Safecast/Safecast-Air/images/hardware-instructions/8.png

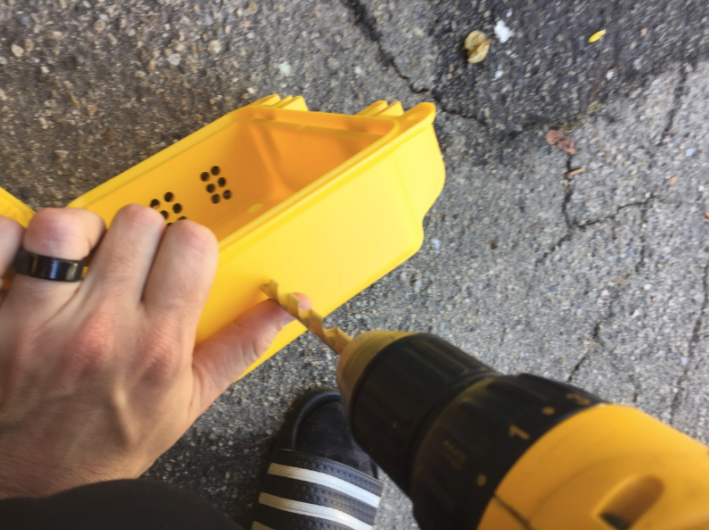
images/hardware-instructions/8.png
