Safecast/Safecast-Air/images/hardware-instructions/9.png

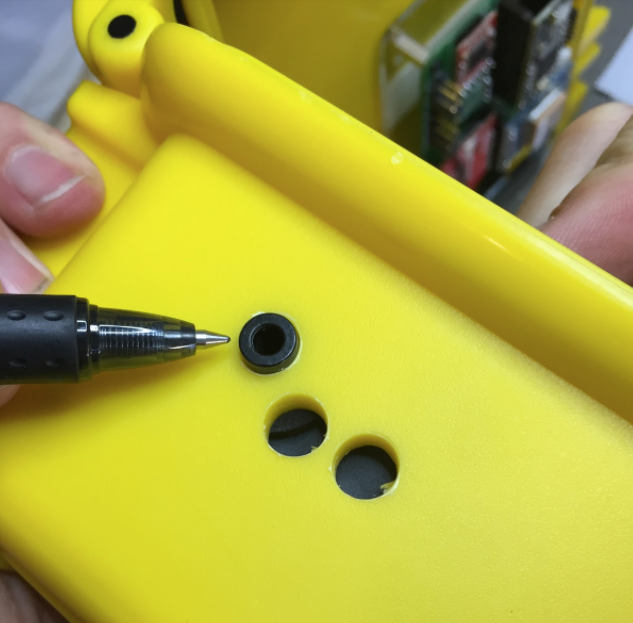
images/hardware-instructions/9.png
