Safecast/Safecast-Air/images/hardware-instructions/10.png

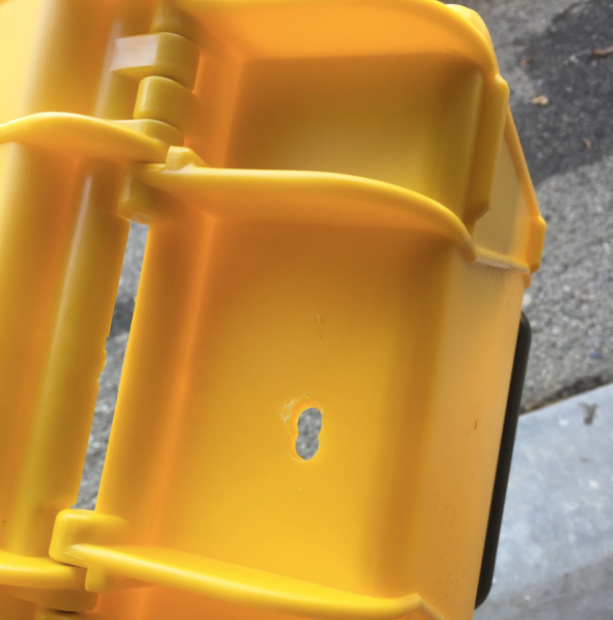
images/hardware-instructions/10.png
