Safecast/Safecast-Air/images/hardware-instructions/11.png

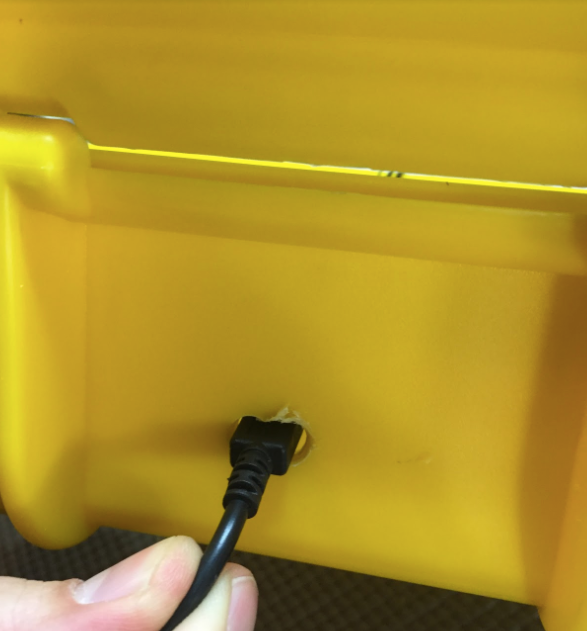
images/hardware-instructions/11.png
