Safecast/Safecast-Air/images/hardware-instructions/13.png

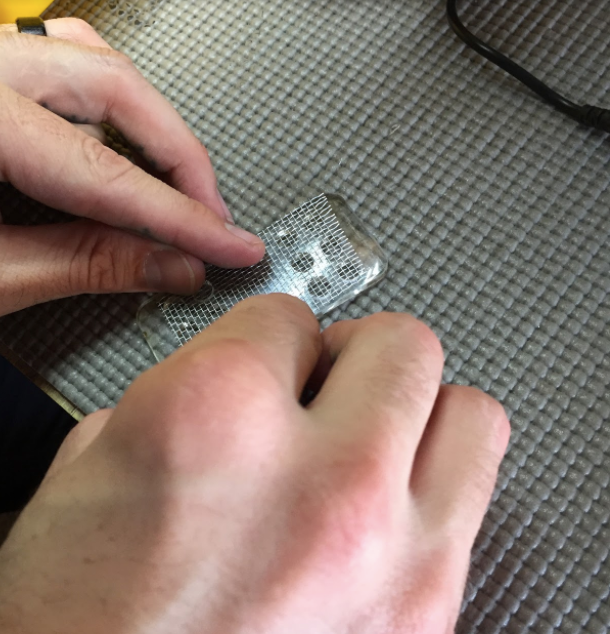
images/hardware-instructions/13.png
