Safecast/Safecast-Air/images/hardware-instructions/14.png

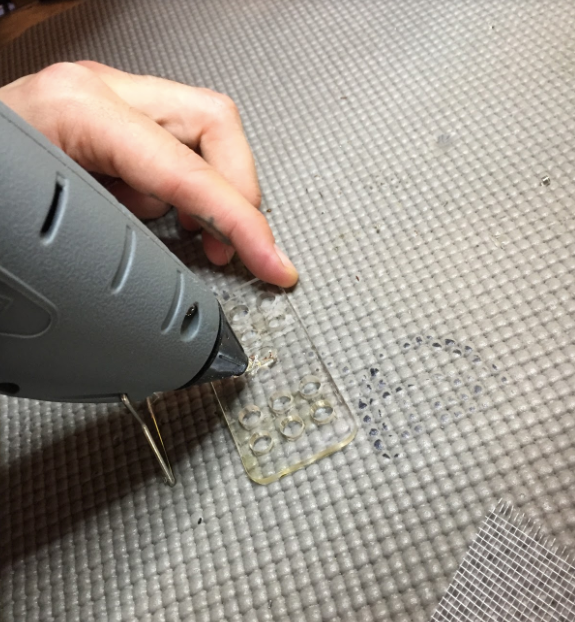
images/hardware-instructions/14.png
