Safecast/Safecast-Air/images/hardware-instructions/15.png

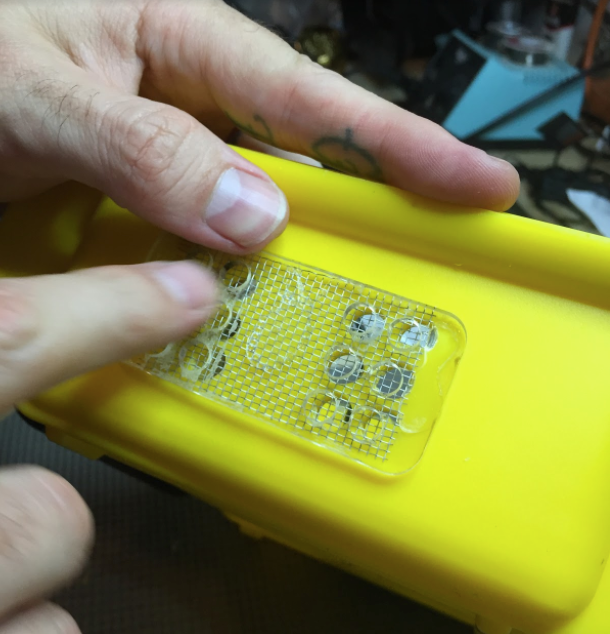
images/hardware-instructions/15.png
