Safecast/Safecast-Air/images/hardware-instructions/16.png

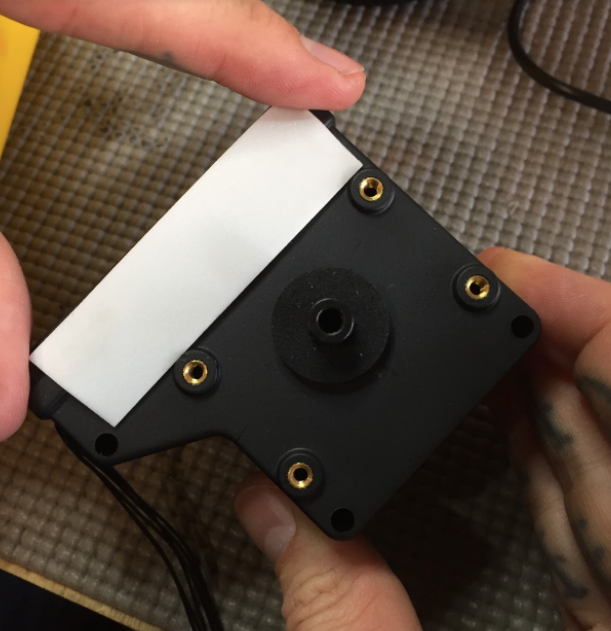
images/hardware-instructions/16.png
