Safecast/Safecast-Air/images/hardware-instructions/17.png

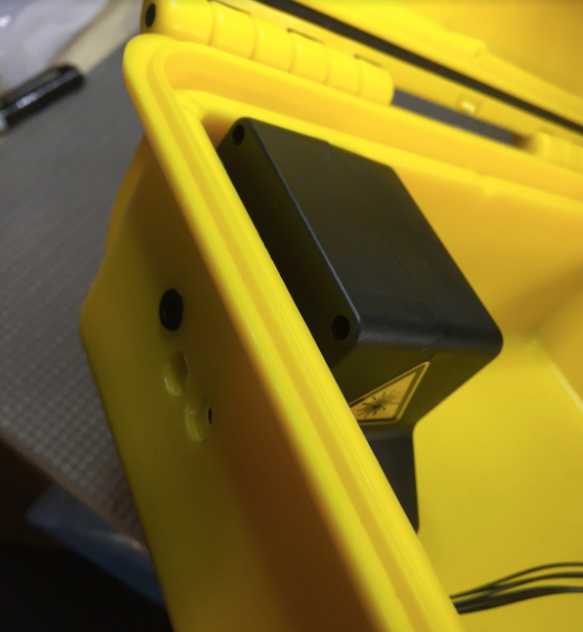
images/hardware-instructions/17.png
