Safecast/Safecast-Air/images/hardware-instructions/18.png

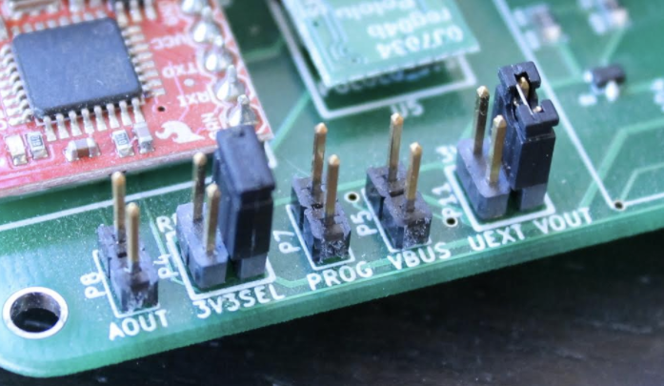
images/hardware-instructions/18.png
