Safecast/Safecast-Air/images/hardware-instructions/19.png

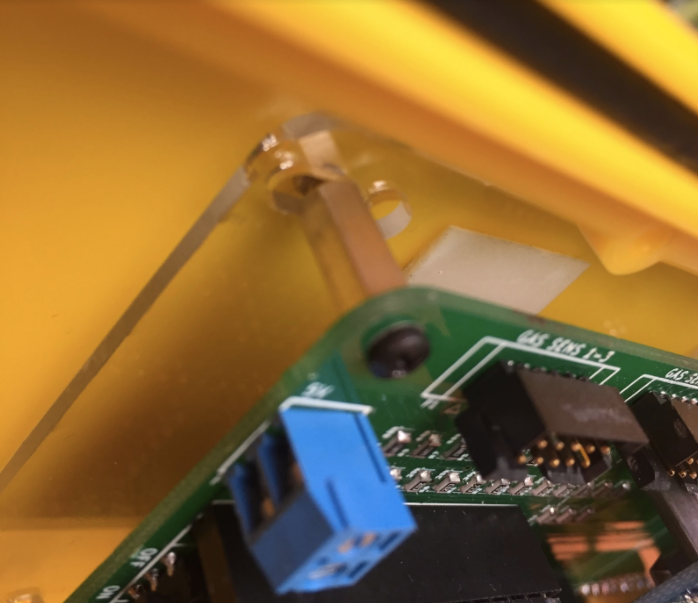
images/hardware-instructions/19.png
