Safecast/Safecast-Air/images/hardware-instructions/20.png

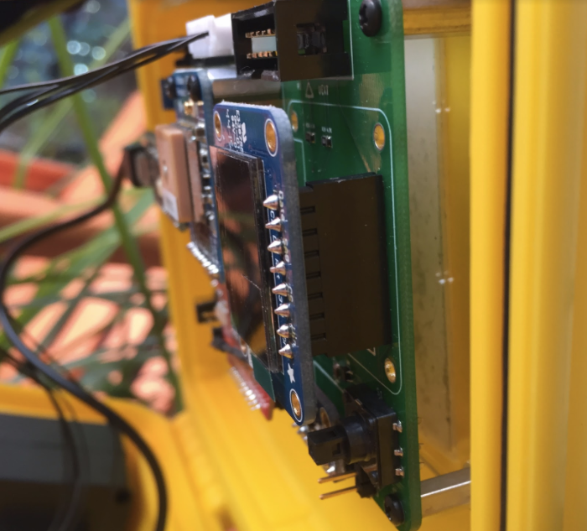
images/hardware-instructions/20.png
