Safecast/Safecast-Air/images/hardware-instructions/21.png

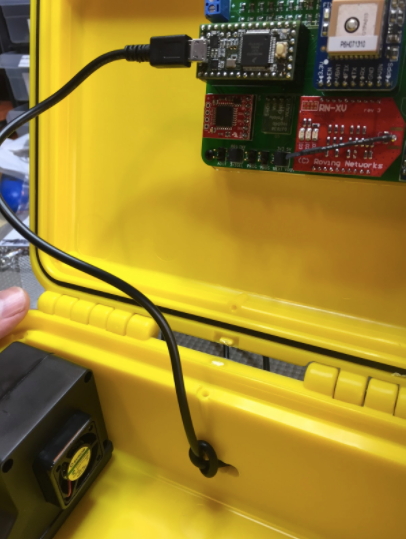
images/hardware-instructions/21.png
