Safecast/Safecast-Air/images/hardware-instructions/22.png

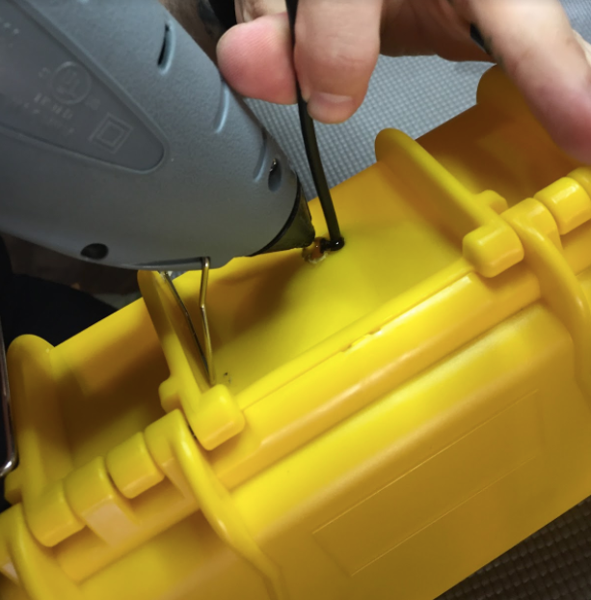
images/hardware-instructions/22.png
