Safecast/Safecast-Air/images/hardware-instructions/23.png

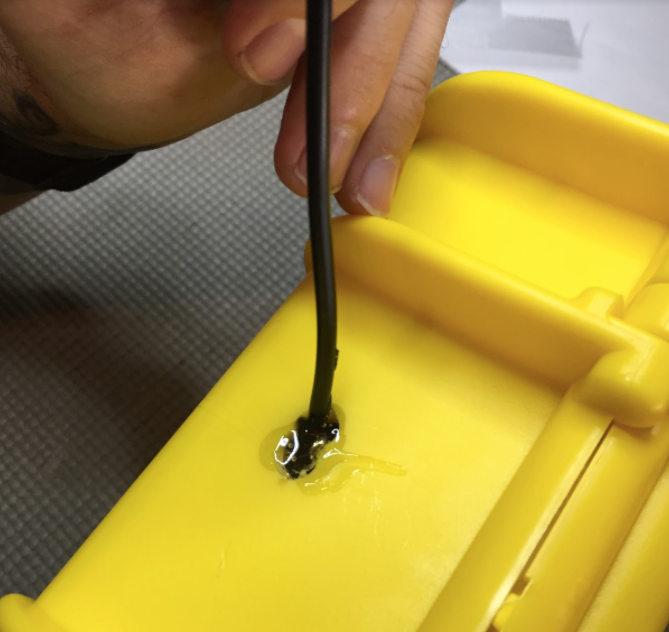
images/hardware-instructions/23.png
