Safecast/Safecast-Air/images/hardware-instructions/24.png

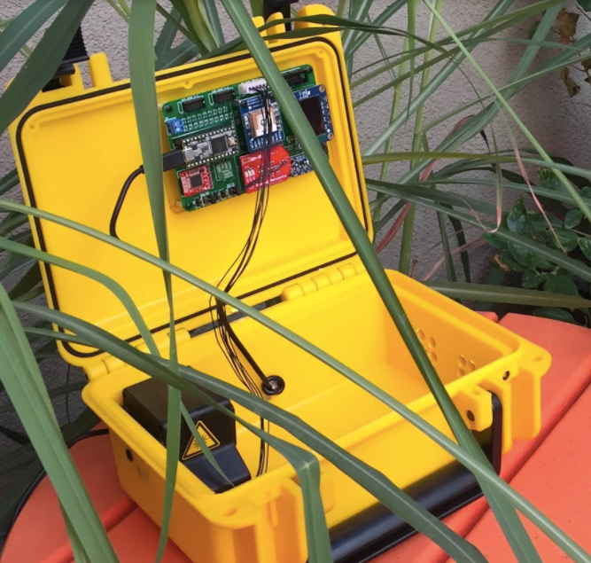
images/hardware-instructions/24.png
