Safecast/Safecast-Air/images/teensy-install.png

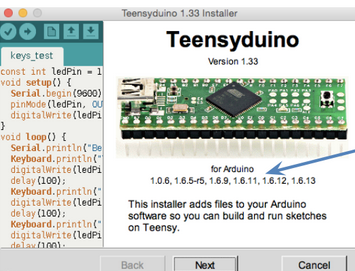
images/teensy-install.png
