Safecast/Safecast-Air/firmware/safecast_air/pm_sensor_param.h

#ifndef PM_SENSOR_PARAM_H
#define PM_SENSOR_PARAM_H

enum ParticleType {SmallParticle=0, LargeParticle, NumParticleType};

struct PMSensorParam
{
    int smallParticlePin;
    int largeParticlePin;
    float sensitivity;
    unsigned long sampleWindowDt; // ms

};

#endif
