Safecast/Safecast-Air/firmware/particulate_only/constants.cpp

#include "constants.h" 
#include <Arduino.h>

namespace constants
{
    const String SoftwareVersion = "0.11";
    const String  DeviceName = "air001"; 
    const String ConfigurationFile = "SAFECAST.txt";

    const long USBSerialBaudRate = 115200;
    const unsigned long LoopDelay = 200;

    // Optical particle coutner OPCN2 parameters  
    // spiClock , spiBitOrder, spiDataMode, spiCsPin
    const OPCN2Param DefaultOPCN2Param = {750000, MSBFIRST, SPI_MODE1, 24};
    const OPCN2Ids DefaultOPCN2Ids = {0, 0, 0, 0, 0, 0, 0, 0, 0, {0, 0, 0, 0, 0, 0, 0, 0, 0, 0, 0, 0, 0, 0, 0, 0}};

    // SHT31 Temperature/Humidity sensor parameters
    extern const int SHT31Address = 0x44;

    // OLED Dislay settings
    const int DisplayDC = 5;
    const int DisplayCS = 3;
    const int DisplayReset = 4;
    const SPISettings DisplaySPISettings(4000000,MSBFIRST,SPI_MODE0);

    // Openlog parameters
    // baudrate, timeout, eepromAddrLogCnt, resetPin, *serialPtr 
    const OpenlogParam DefaultOpenlogParam = {115200, 500, 0, 6, &Serial3} ;

    // Load configuration parameters
    extern const int NumLoadConfigTrys = 20;

    // Logger parameters 
    // writeLogPeriod(s), dataSamplePeriod(s), baudRate 
    const LoggerParam DefaultLoggerParam = {300, 30, 115200};
    //const LoggerParam DefaultLoggerParam = {60, 30, 115200}; // Testing
    const int RandomSeedAinPin = A12;

    // Wifi parameters 
    // pwrPin, pwerOnDelay, pwrOffDelay, baudrate, *serialPtr
    const WifiParam DefaultWifiParam = {31, 4000, 1000, 9600, &Serial2};
}
