Safecast/Safecast-Air/notes/sd_card_example/CONFIG.TXT

115200,26,3,2,0,0,0
baud,escape,esc#,mode,verb,echo,ignoreRX
